matnalopez2/electronica-aplicada-3/Entregables/Recursos/Circuito_ideal_inicial.jpg

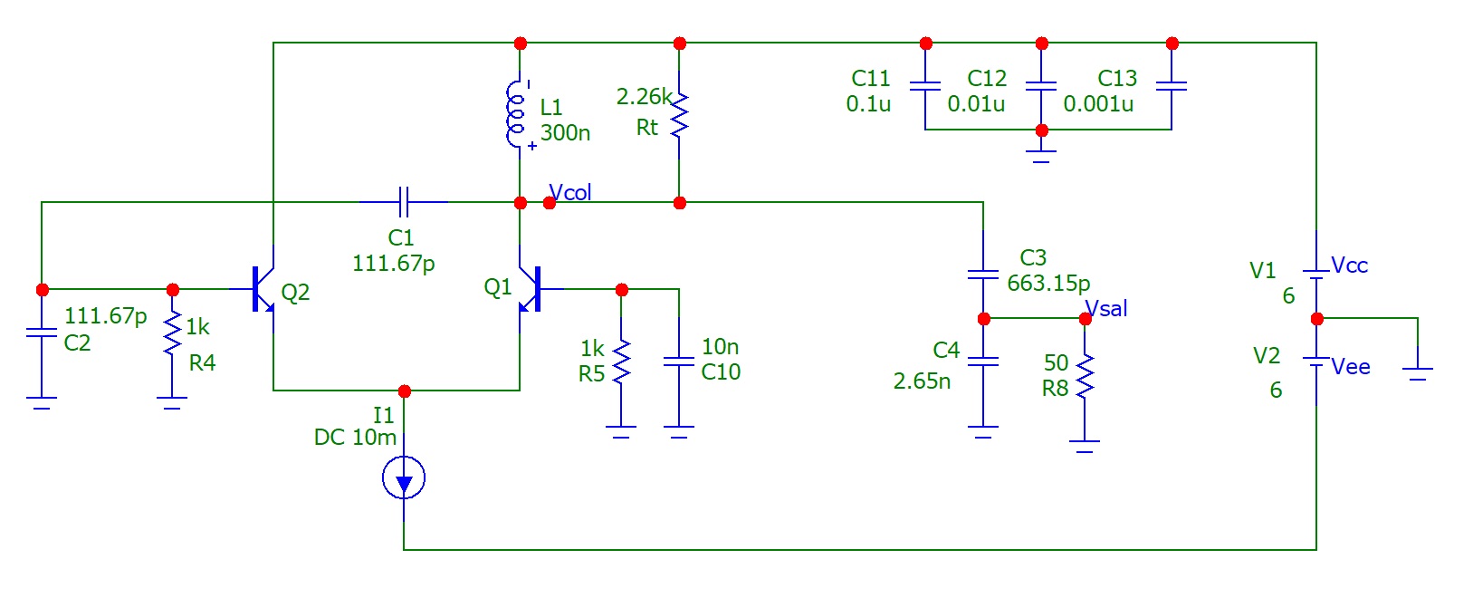
Entregables/Recursos/Circuito_ideal_inicial.jpg
