matnalopez2/electronica-aplicada-3/Recursos/01-Oscilador ideal/01_Circuito_ideal_inicial.jpg

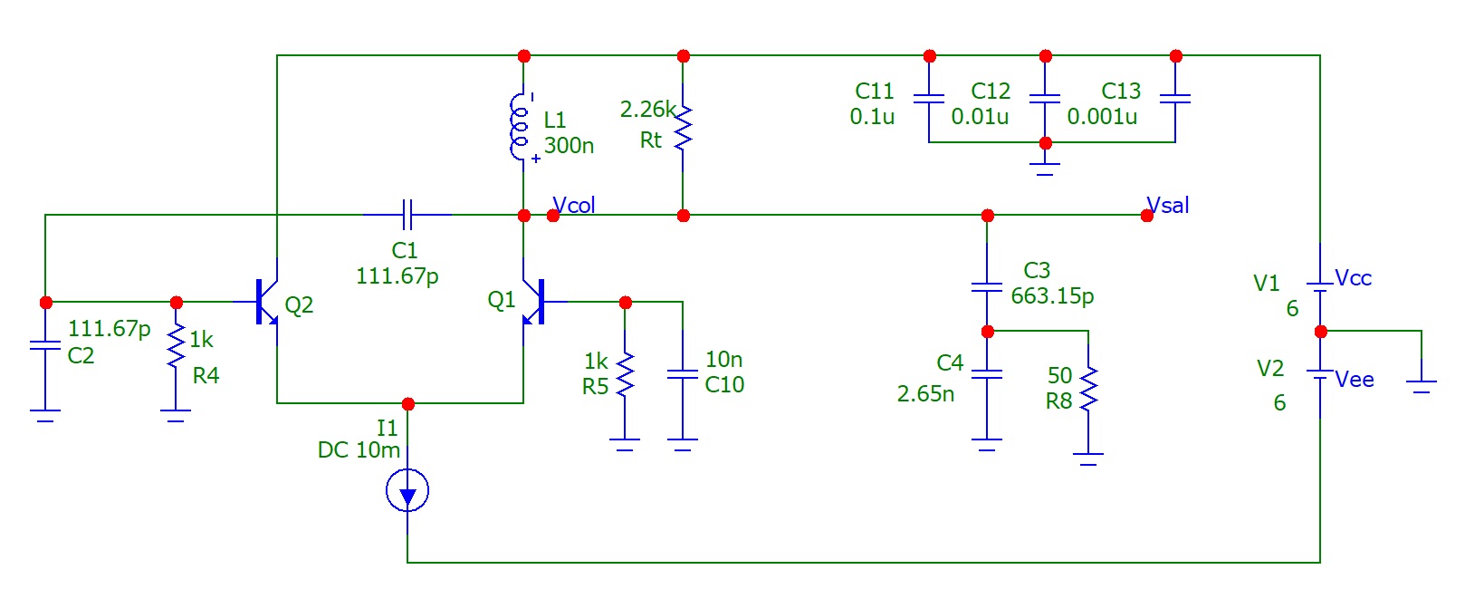
Recursos/01-Oscilador ideal/01_Circuito_ideal_inicial.jpg
