matnalopez2/electronica-aplicada-3/Recursos/01-Oscilador ideal/01_Circuito_ideal_inicial_v2.jpg

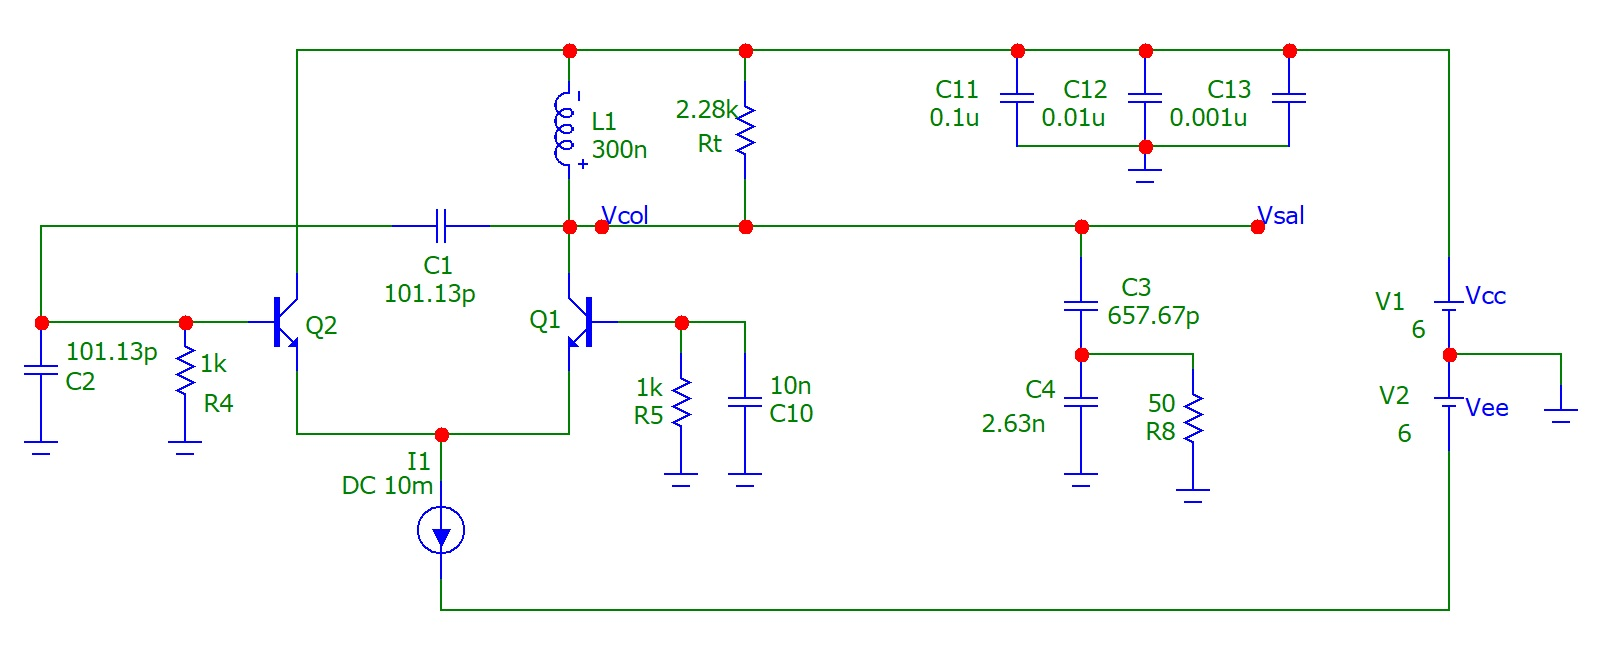
Recursos/01-Oscilador ideal/01_Circuito_ideal_inicial_v2.jpg
