matnalopez2/electronica-aplicada-3/Recursos/01-Oscilador ideal/02_circuito_ideal_con_fuente_ideal_Vcol.jpg

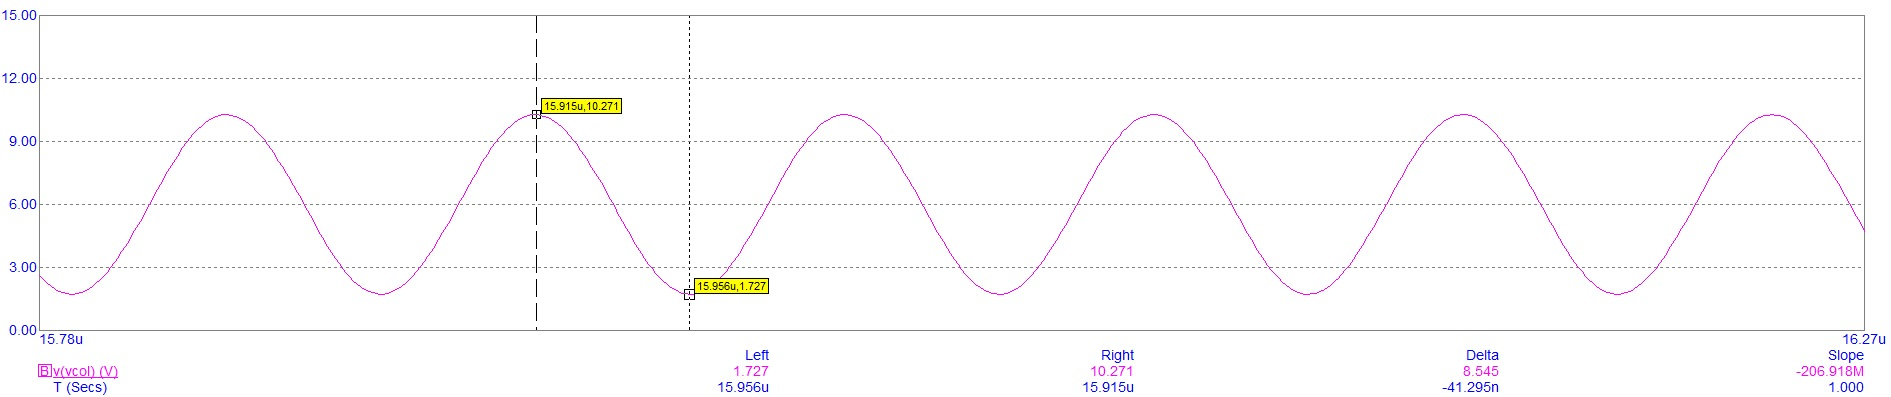
Recursos/01-Oscilador ideal/02_circuito_ideal_con_fuente_ideal_Vcol.jpg
