matnalopez2/electronica-aplicada-3/Recursos/01-Oscilador ideal/03_circuito_ideal_con_fuente_ideal_Vsal.jpg

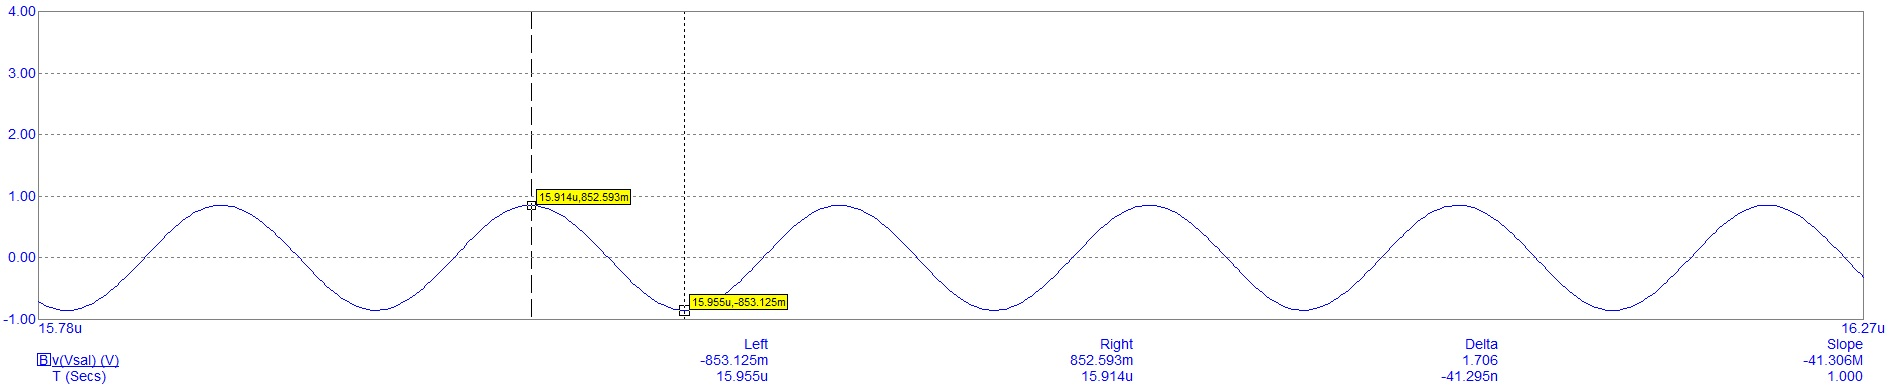
Recursos/01-Oscilador ideal/03_circuito_ideal_con_fuente_ideal_Vsal.jpg
