matnalopez2/electronica-aplicada-3/Recursos/03-Circuito ideal con valores comerciales/03_circuito_ideal_valores_comerciales_Vcol.jpg

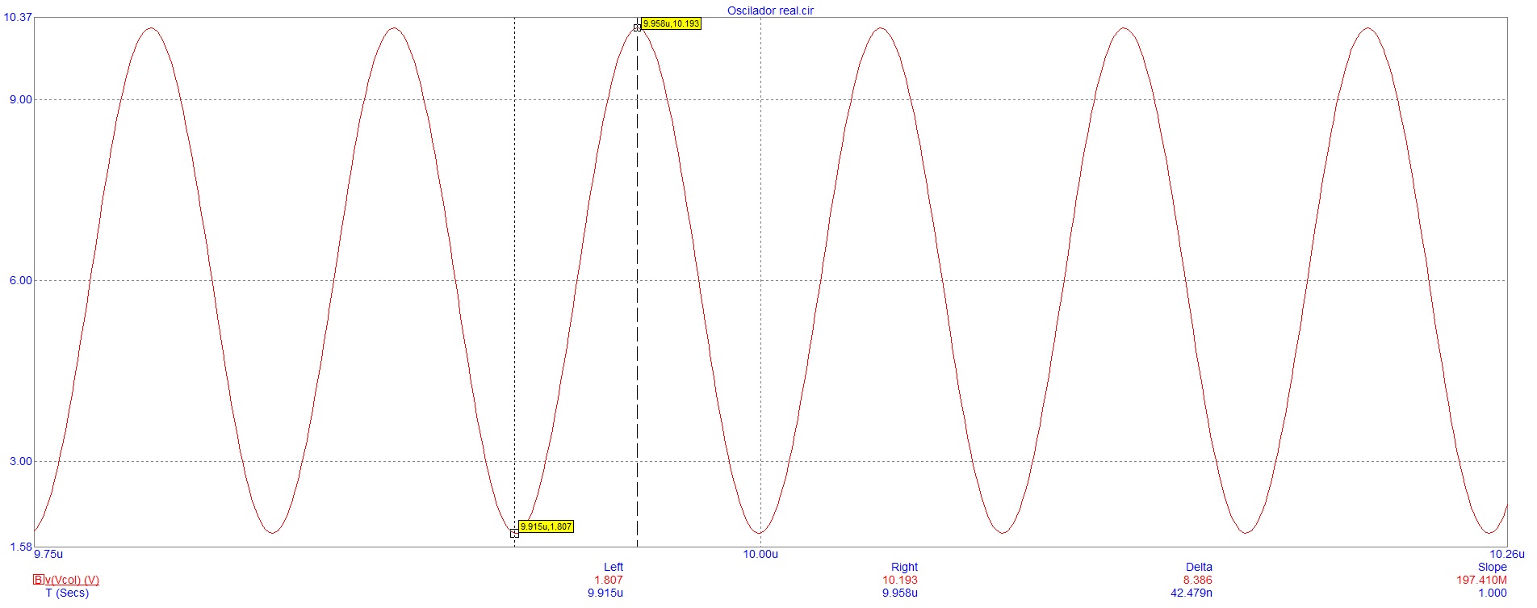
Recursos/03-Circuito ideal con valores comerciales/03_circuito_ideal_valores_comerciales_Vcol.jpg
