matnalopez2/electronica-aplicada-3/Recursos/03-Circuito ideal con valores comerciales/04_circuito_ideal_valores_comerciales_Vsal.jpg

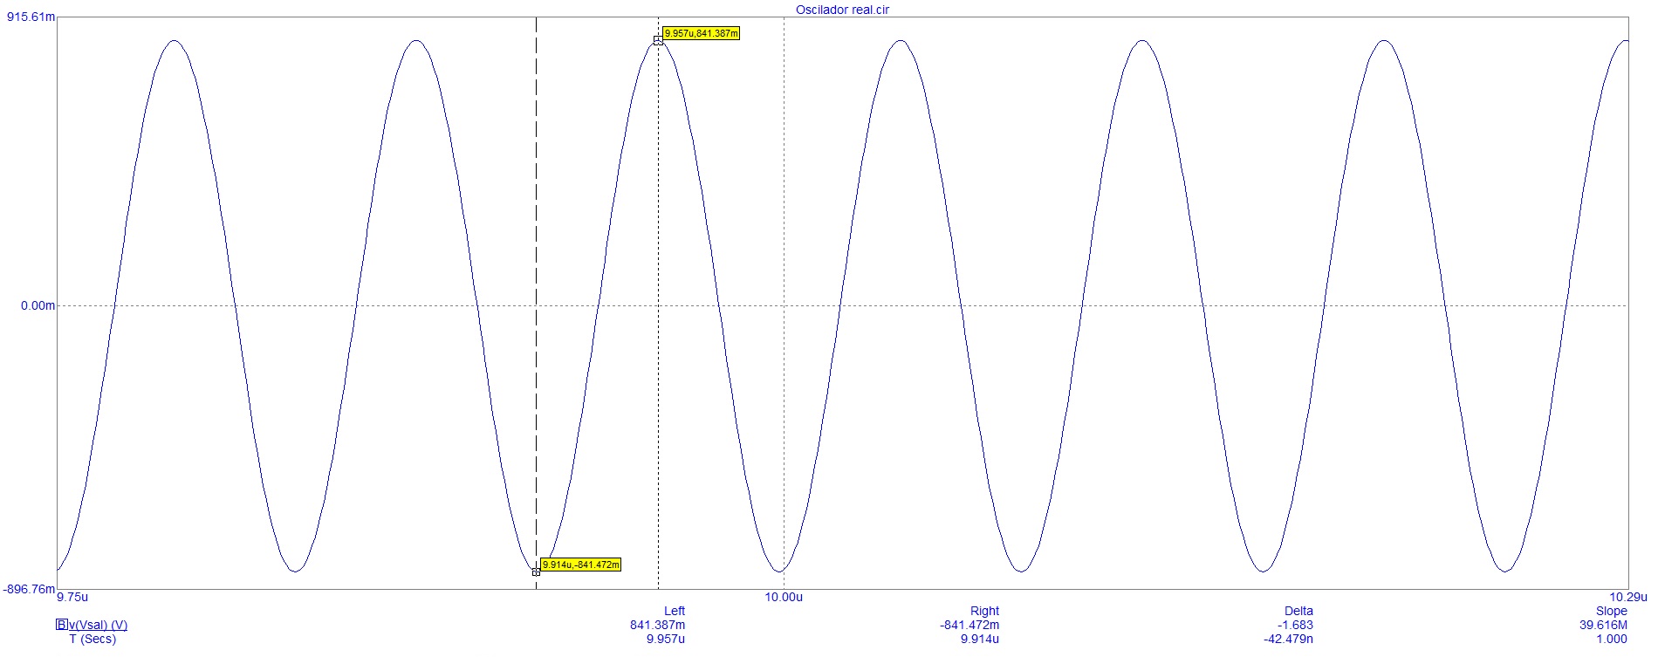
Recursos/03-Circuito ideal con valores comerciales/04_circuito_ideal_valores_comerciales_Vsal.jpg
