matnalopez2/electronica-aplicada-3/Recursos/05-Oscilador con mediciones FRA/01_esquematico.jpg

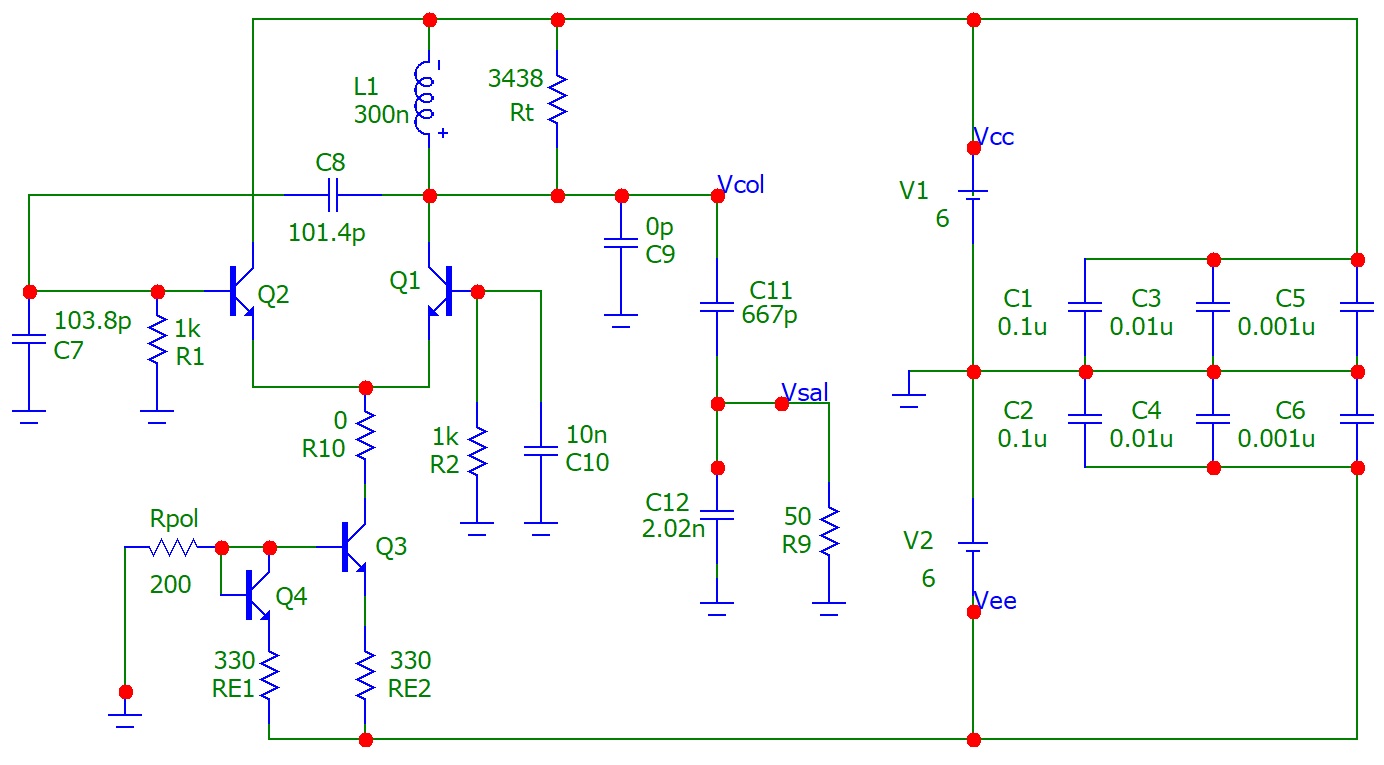
Recursos/05-Oscilador con mediciones FRA/01_esquematico.jpg
