matnalopez2/electronica-aplicada-3/Recursos/05-Oscilador con mediciones FRA/03_colector_transientConFrecuencia.jpg

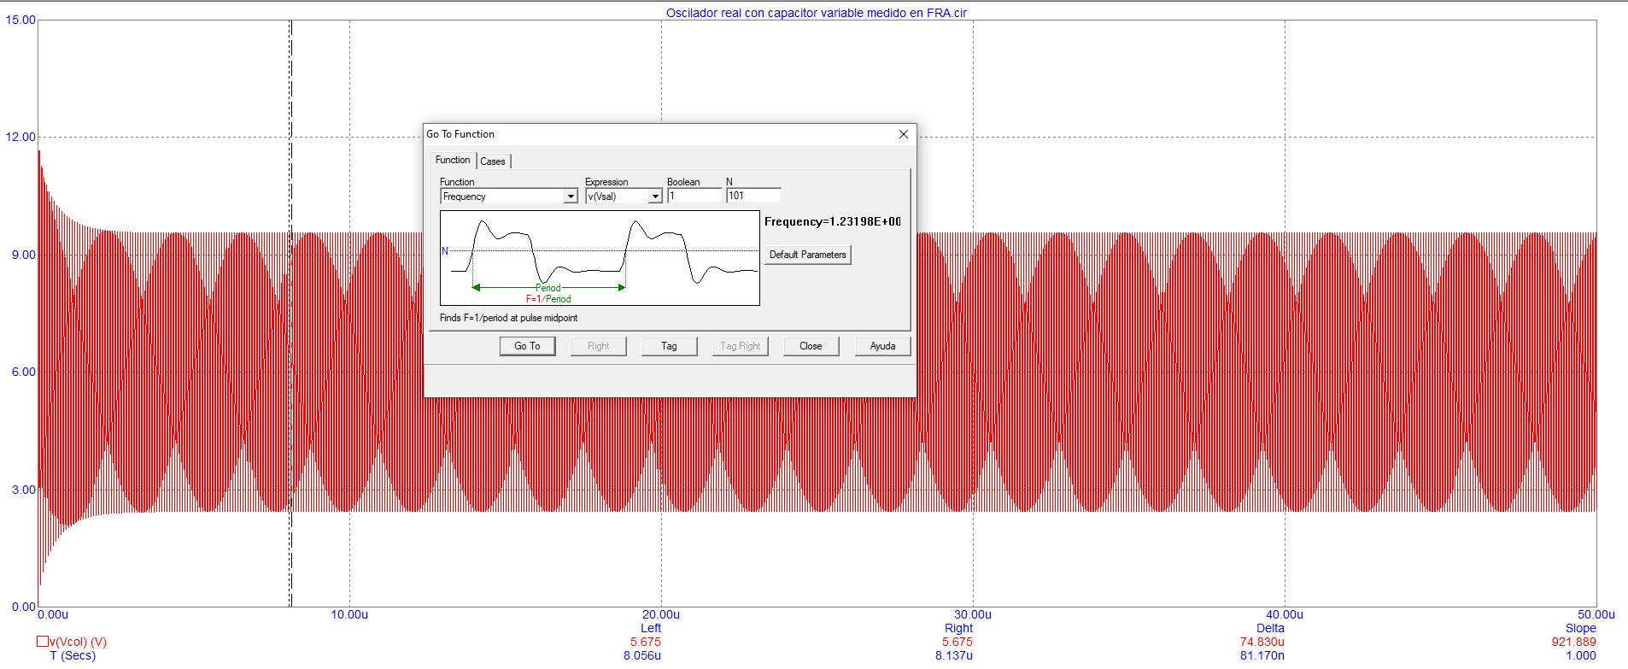
Recursos/05-Oscilador con mediciones FRA/03_colector_transientConFrecuencia.jpg
