matnalopez2/electronica-aplicada-3/Recursos/05-Oscilador con mediciones FRA/04_colector_frecuencia.jpg

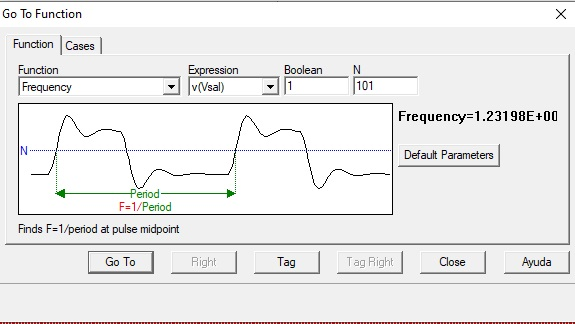
Recursos/05-Oscilador con mediciones FRA/04_colector_frecuencia.jpg
