matnalopez2/electronica-aplicada-3/Recursos/05-Oscilador con mediciones FRA/05_colector_cicloConCursores.jpg

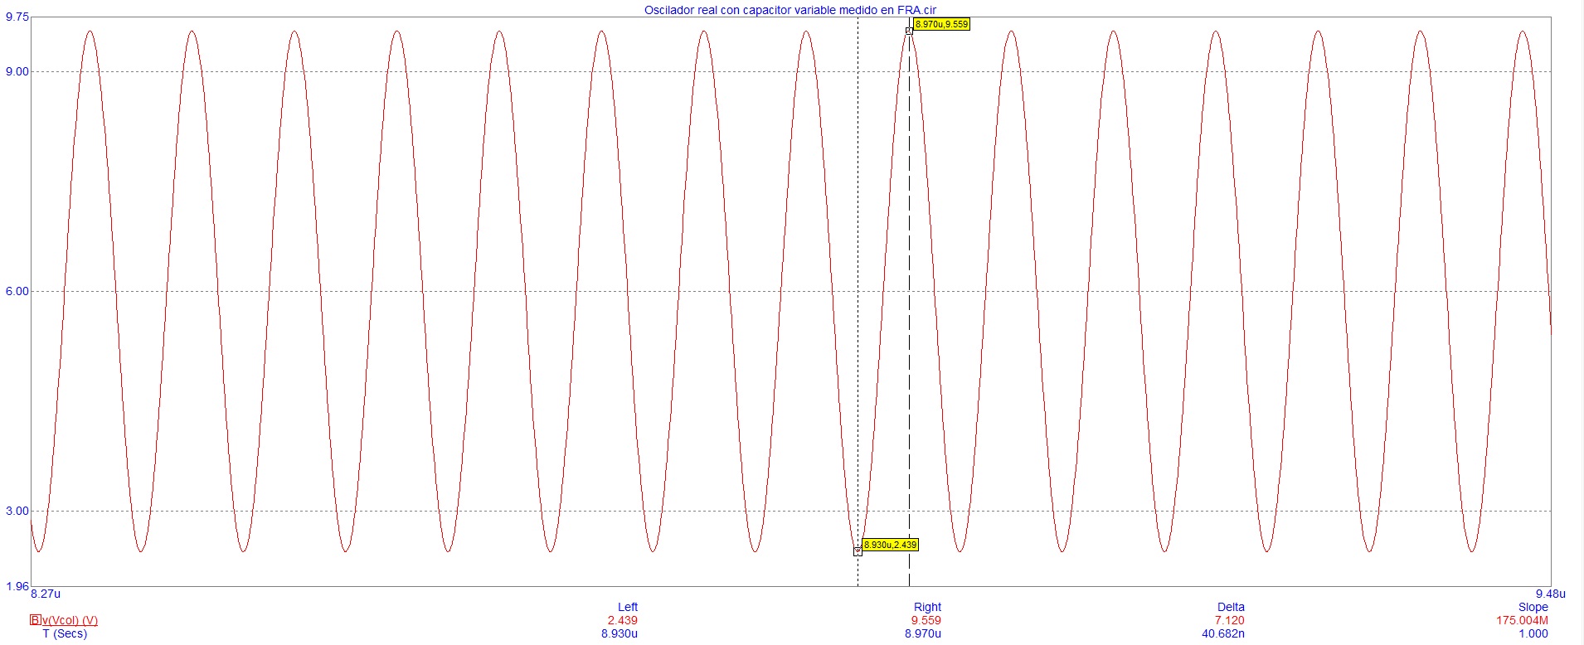
Recursos/05-Oscilador con mediciones FRA/05_colector_cicloConCursores.jpg
