matnalopez2/electronica-aplicada-3/Recursos/05-Oscilador con mediciones FRA/06_colector_cicloConFrecuencia.jpg

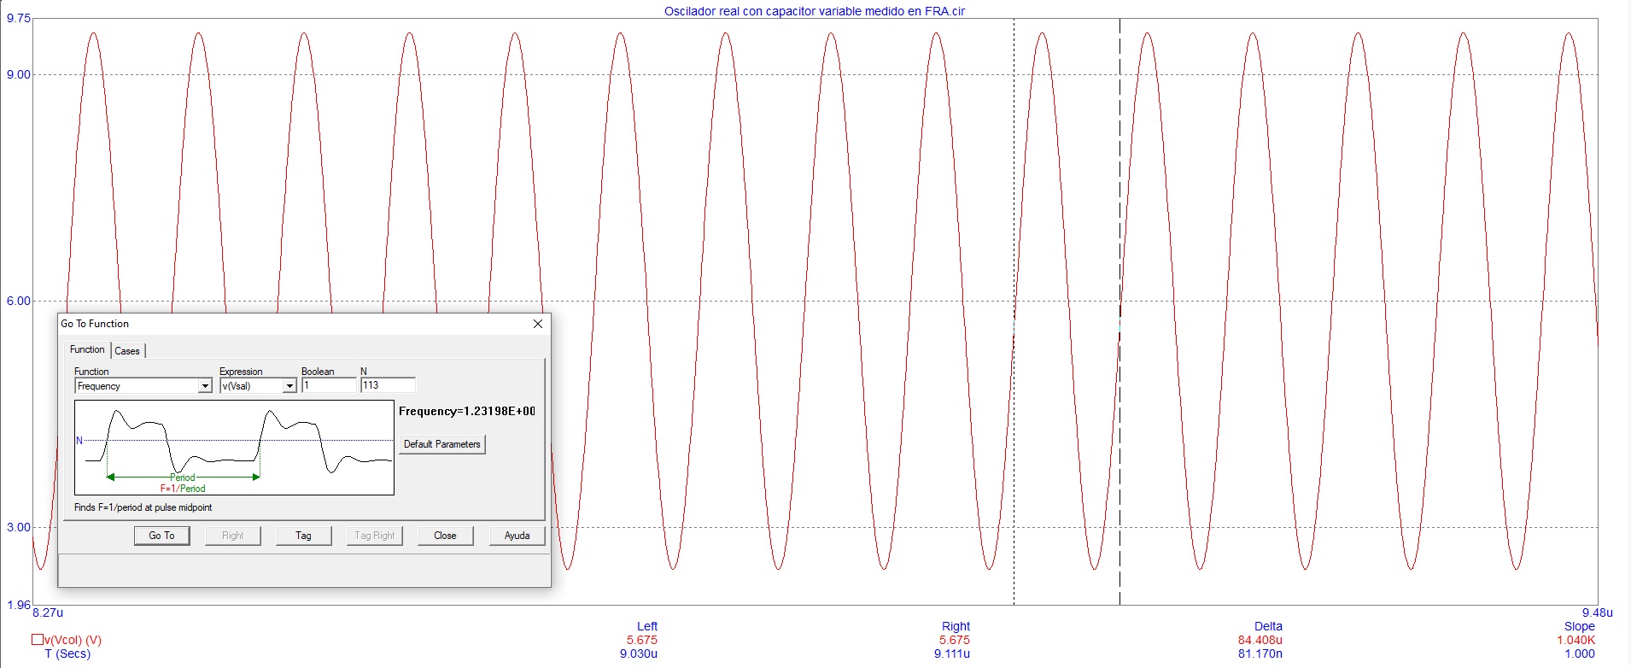
Recursos/05-Oscilador con mediciones FRA/06_colector_cicloConFrecuencia.jpg
