matnalopez2/electronica-aplicada-3/Recursos/05-Oscilador con mediciones FRA/07_colector_picosPositivos.jpg

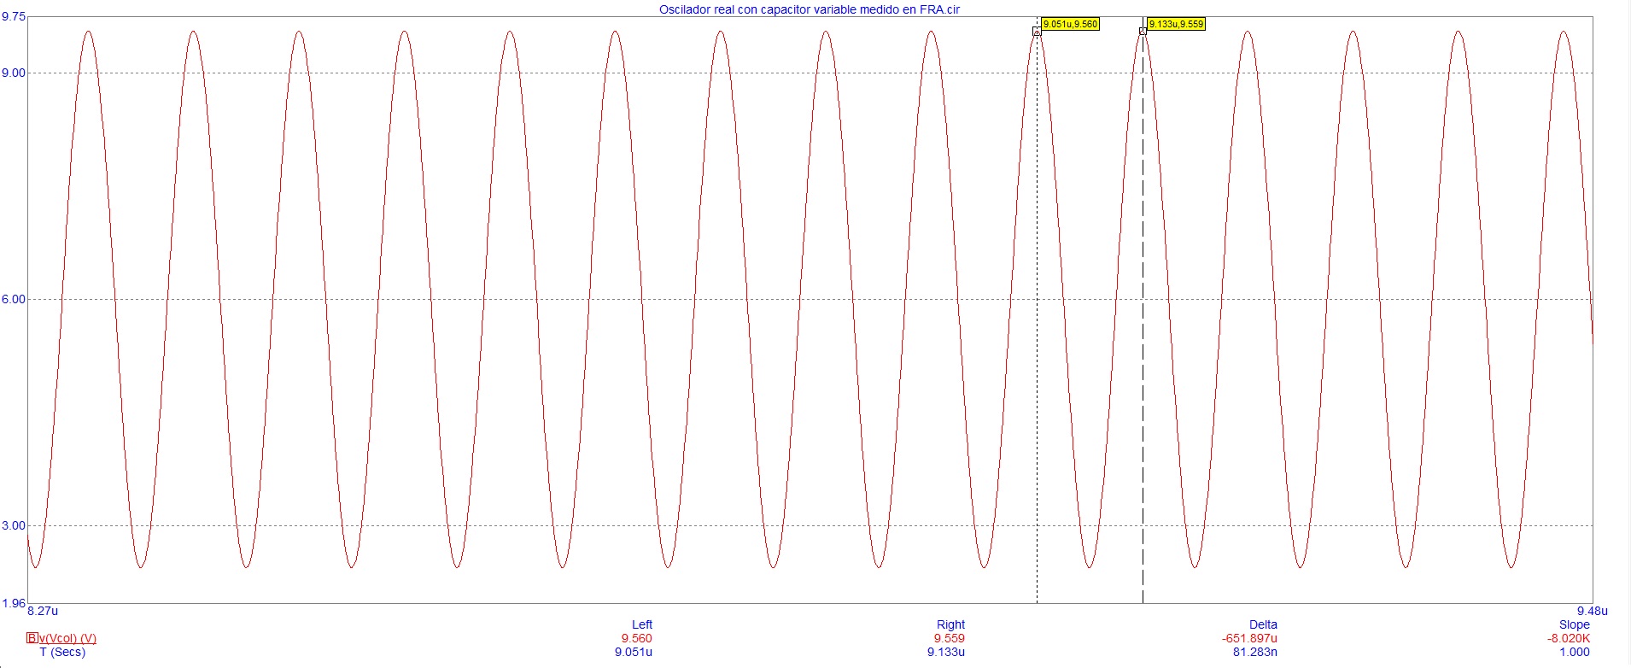
Recursos/05-Oscilador con mediciones FRA/07_colector_picosPositivos.jpg
