matnalopez2/electronica-aplicada-3/Recursos/05-Oscilador con mediciones FRA/08_salida_transient.jpg

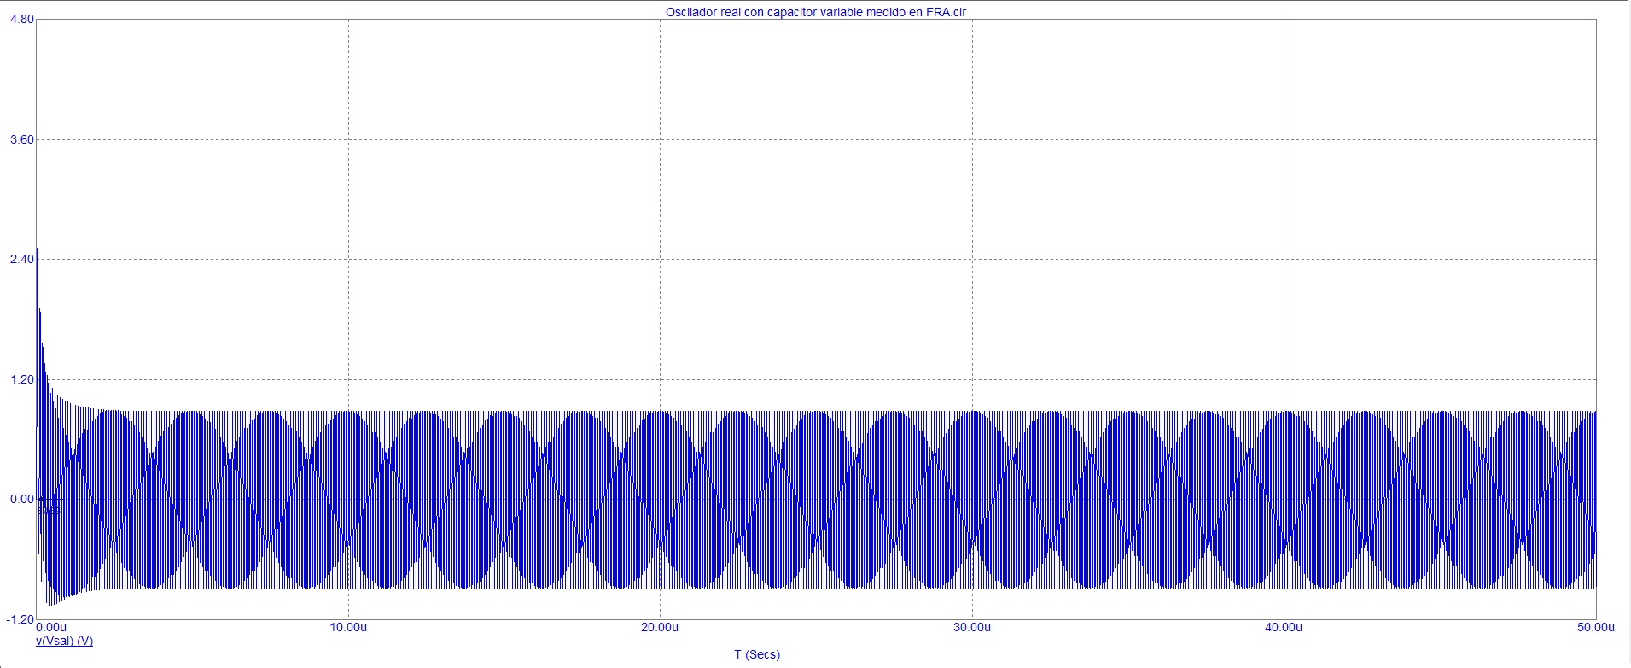
Recursos/05-Oscilador con mediciones FRA/08_salida_transient.jpg
