matnalopez2/electronica-aplicada-3/Recursos/05-Oscilador con mediciones FRA/11_salida_cicloConCursores.jpg

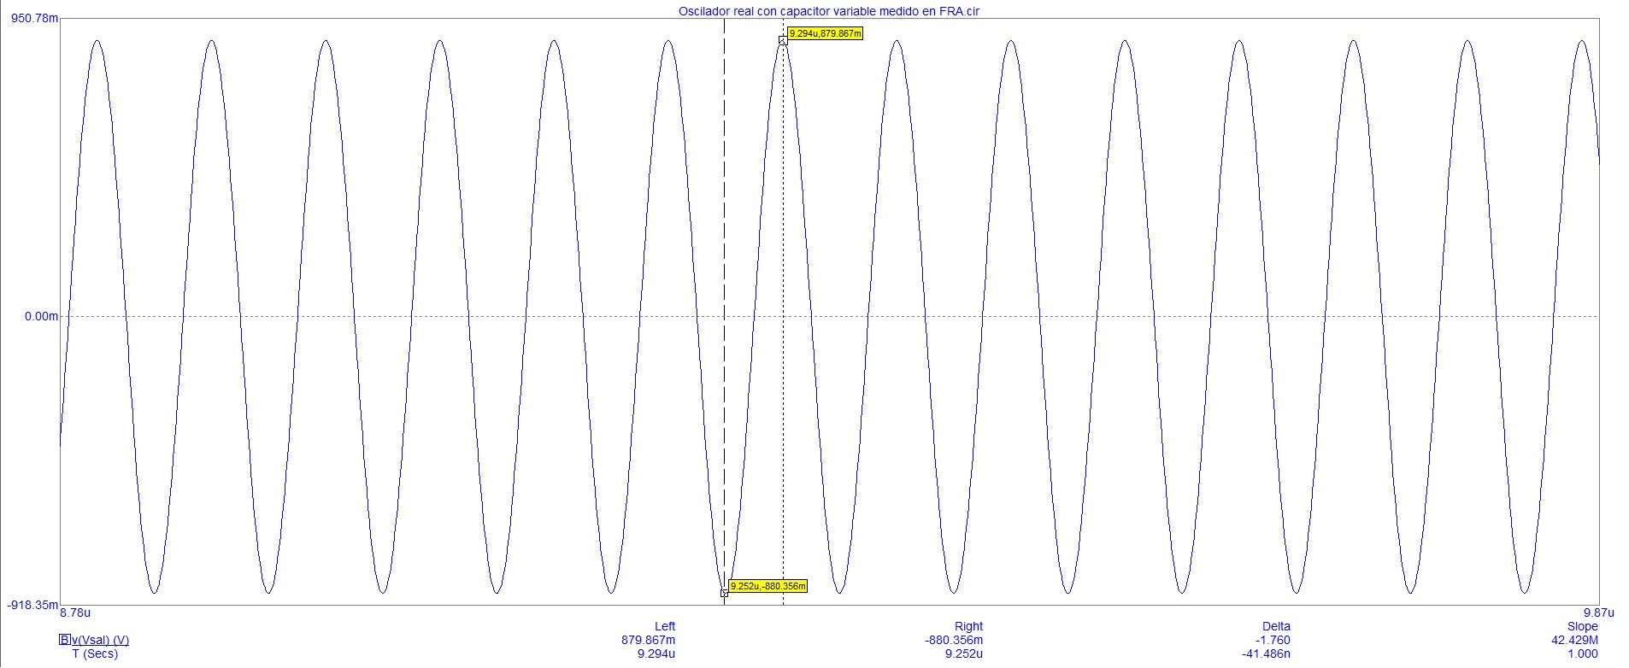
Recursos/05-Oscilador con mediciones FRA/11_salida_cicloConCursores.jpg
