matnalopez2/electronica-aplicada-3/Recursos/05-Oscilador con mediciones FRA/12_salida_cicloConFrecuencia.jpg

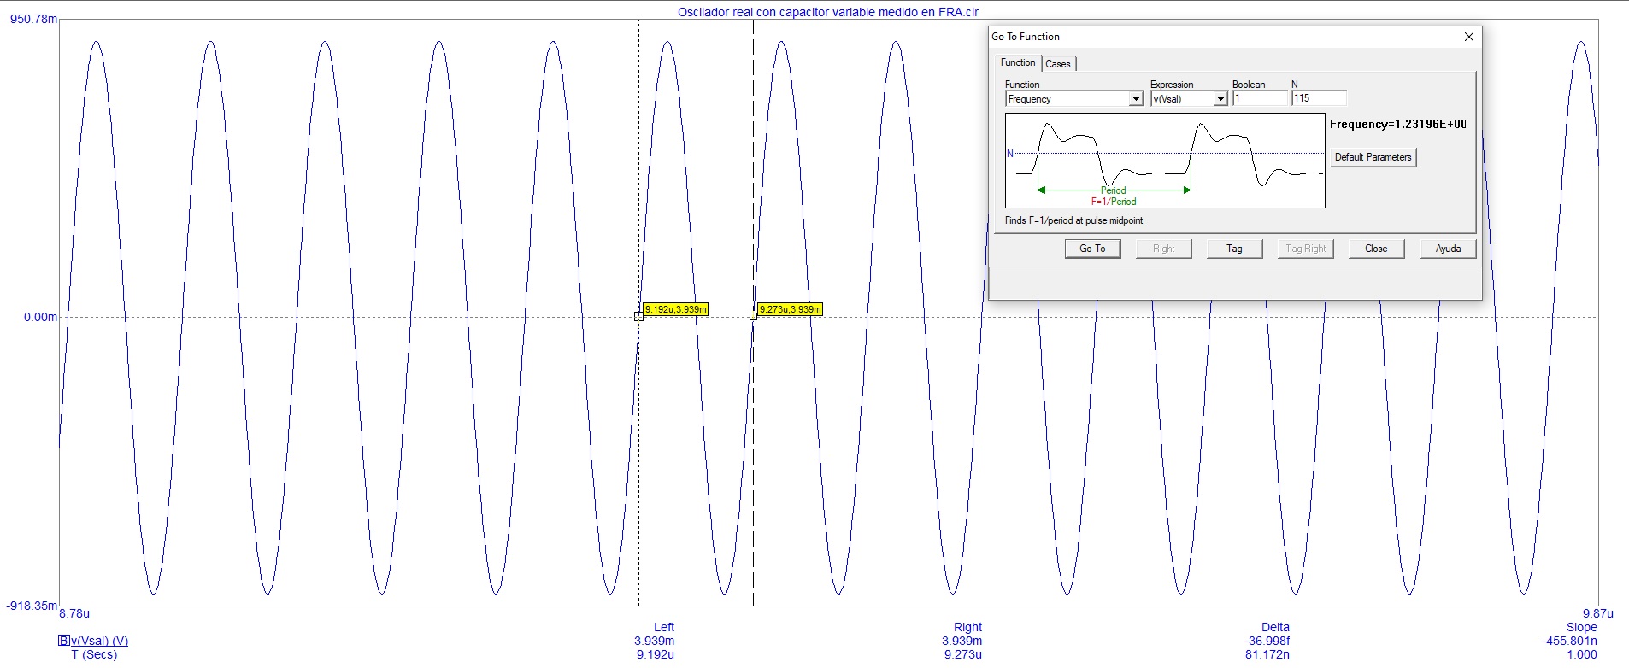
Recursos/05-Oscilador con mediciones FRA/12_salida_cicloConFrecuencia.jpg
