matnalopez2/electronica-aplicada-3/Recursos/05-Oscilador con mediciones FRA/13_salida_picosPositivos.jpg

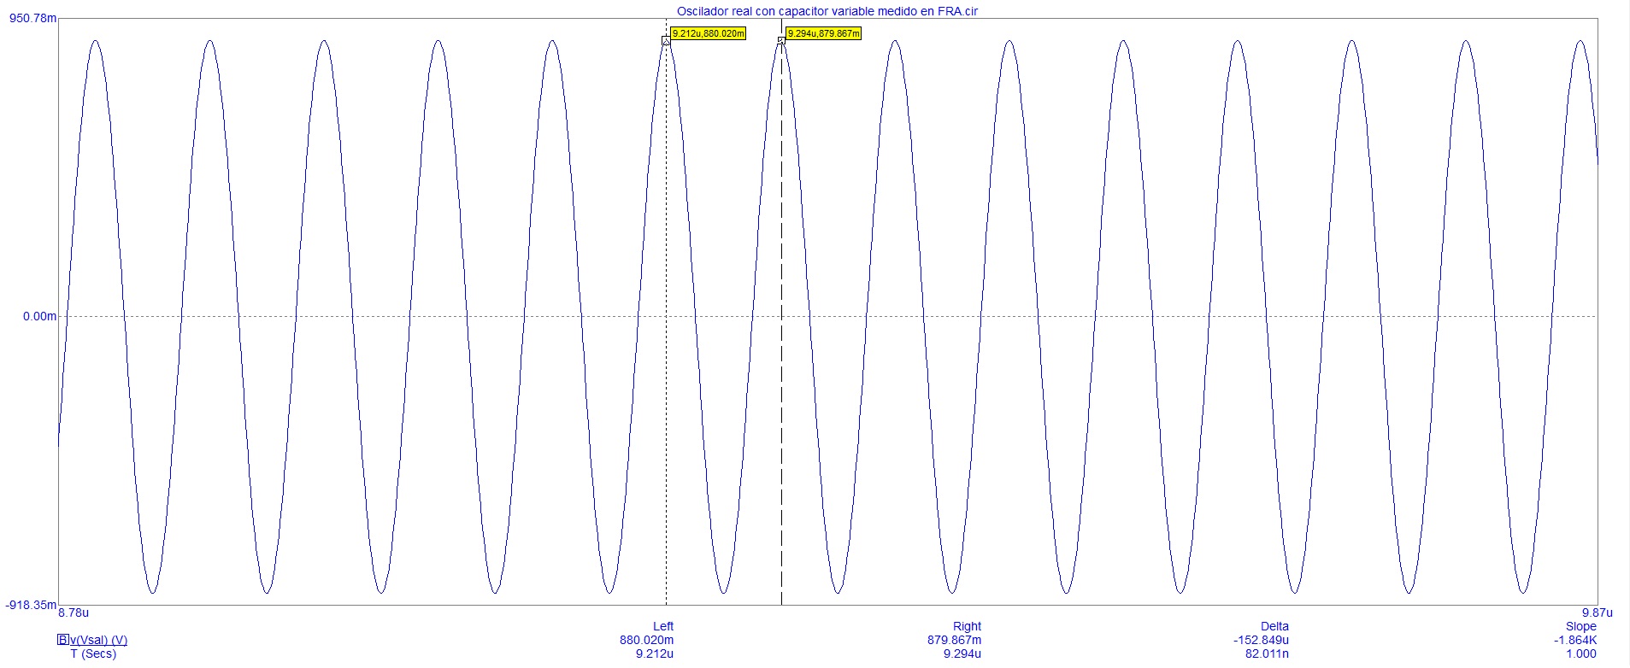
Recursos/05-Oscilador con mediciones FRA/13_salida_picosPositivos.jpg
