matnalopez2/electronica-aplicada-3/Recursos/06-Placa terminada/01_placaSuperior.jpeg

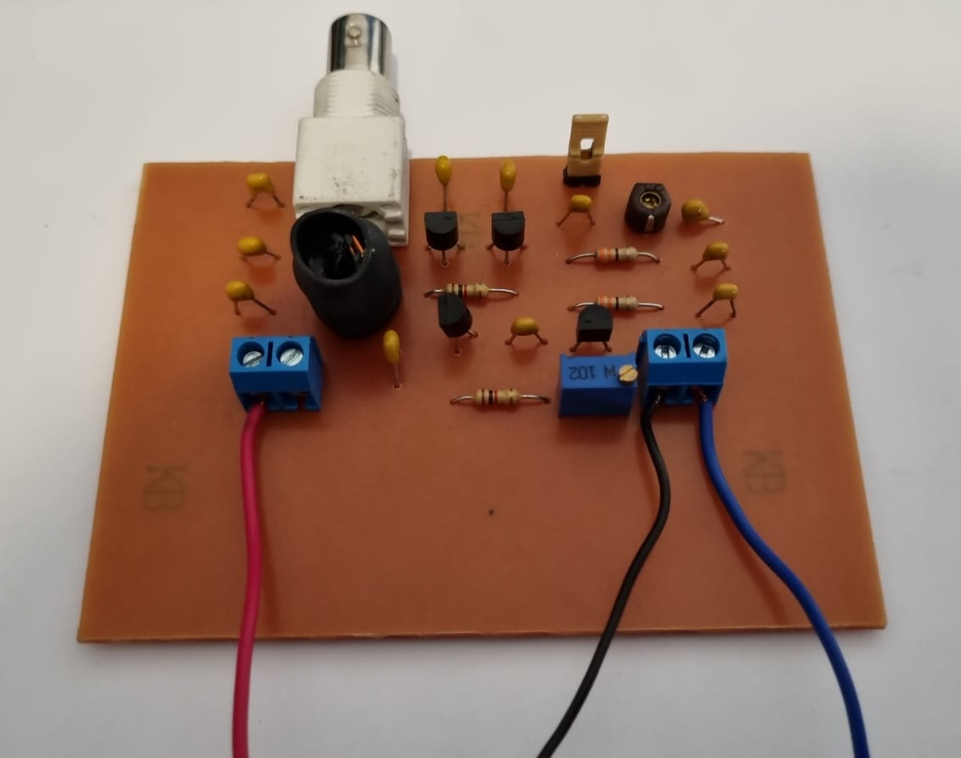
Recursos/06-Placa terminada/01_placaSuperior.jpeg
