matnalopez2/electronica-aplicada-3/Recursos/06-Placa terminada/03_placaPistas.jpeg

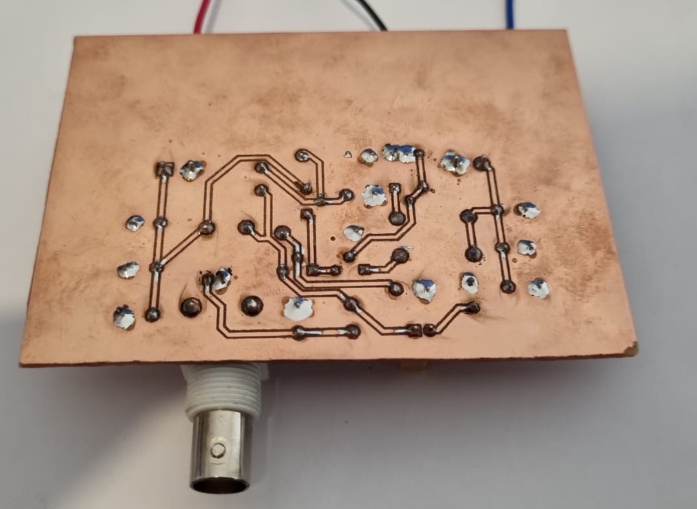
Recursos/06-Placa terminada/03_placaPistas.jpeg
