matnalopez2/electronica-aplicada-3/Recursos/06-Placa terminada/04_placaPistas.jpeg

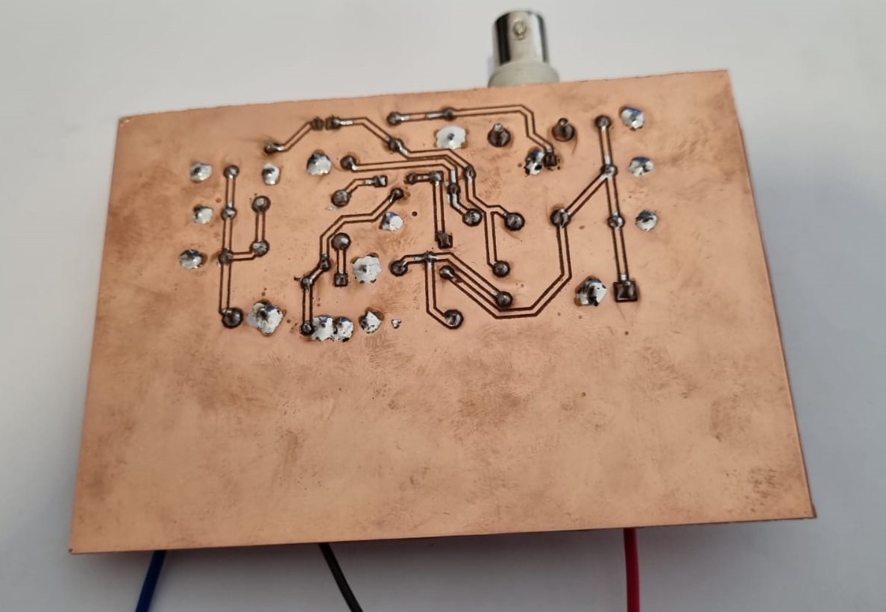
Recursos/06-Placa terminada/04_placaPistas.jpeg
