matnalopez2/electronica-aplicada-3/Recursos/07-Mediciones/1.jpeg

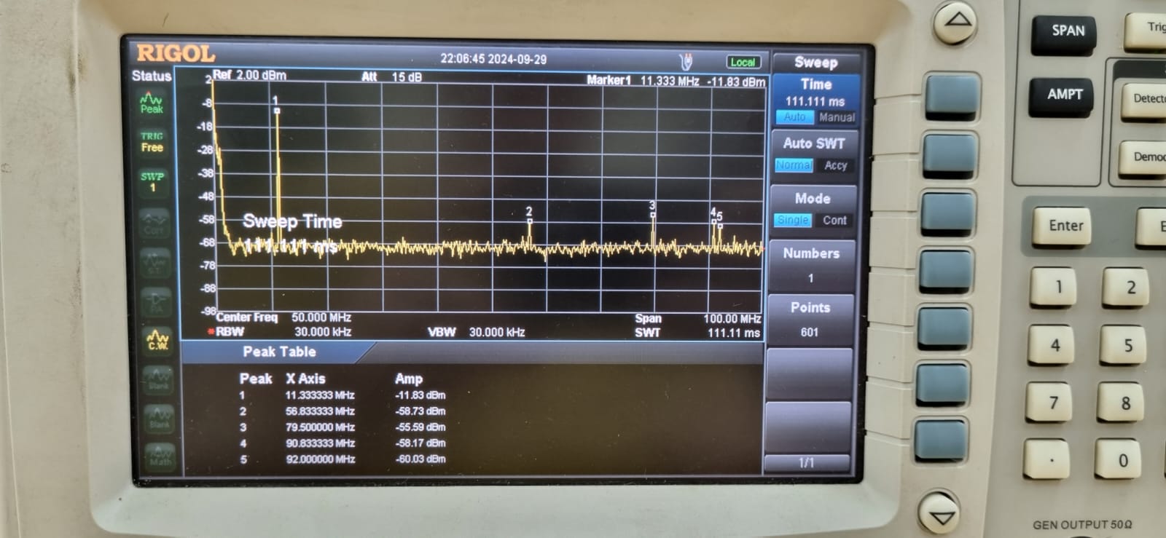
Recursos/07-Mediciones/1.jpeg
