matnalopez2/electronica-aplicada-3/Recursos/07-Mediciones/3.jpeg

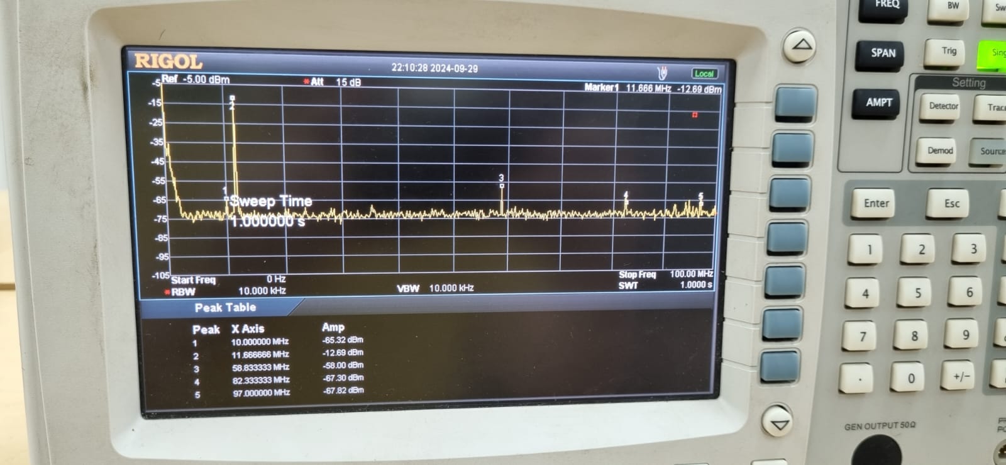
Recursos/07-Mediciones/3.jpeg
