matnalopez2/electronica-aplicada-3/Recursos/07-Mediciones/4_placaSinJumper.jpeg

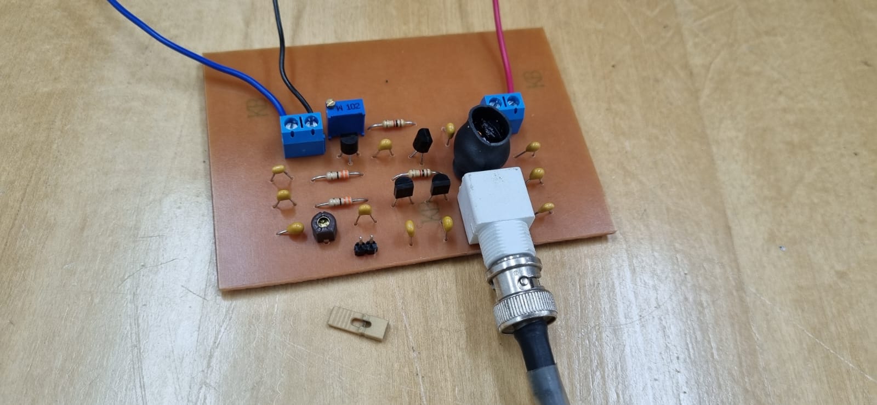
Recursos/07-Mediciones/4_placaSinJumper.jpeg
