matnalopez2/electronica-aplicada-3/Recursos/07-Mediciones/6_instrumentos.jpeg

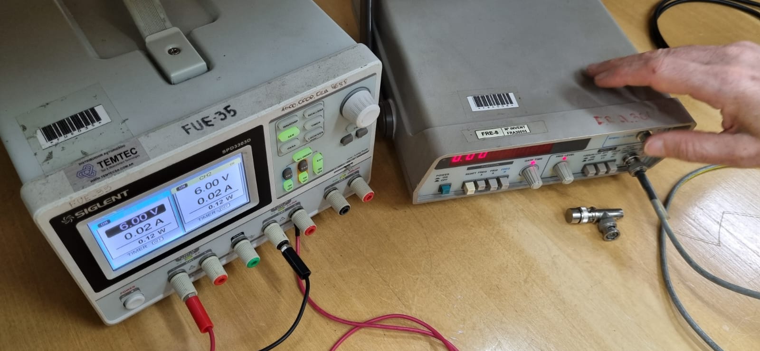
Recursos/07-Mediciones/6_instrumentos.jpeg
