matnalopez2/electronica-aplicada-3/Recursos/07-Mediciones/7_instrumentos.jpeg

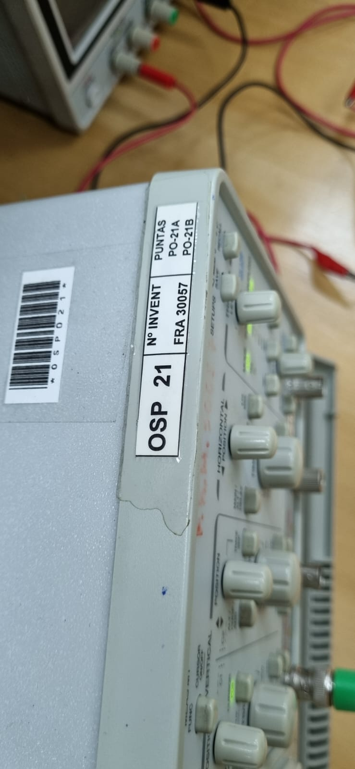
Recursos/07-Mediciones/7_instrumentos.jpeg
