matnalopez2/electronica-aplicada-3/Recursos/07-Mediciones/8_frecuencimetroMaximo.jpeg

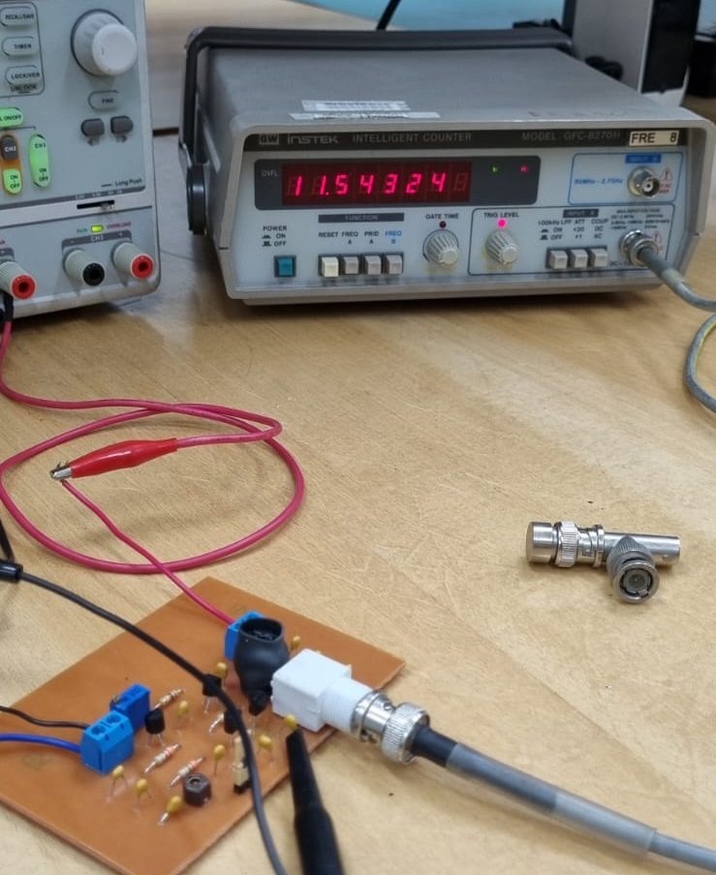
Recursos/07-Mediciones/8_frecuencimetroMaximo.jpeg
