matnalopez2/electronica-aplicada-3/Recursos/07-Mediciones/9_frecuencimetroMinimo.jpeg

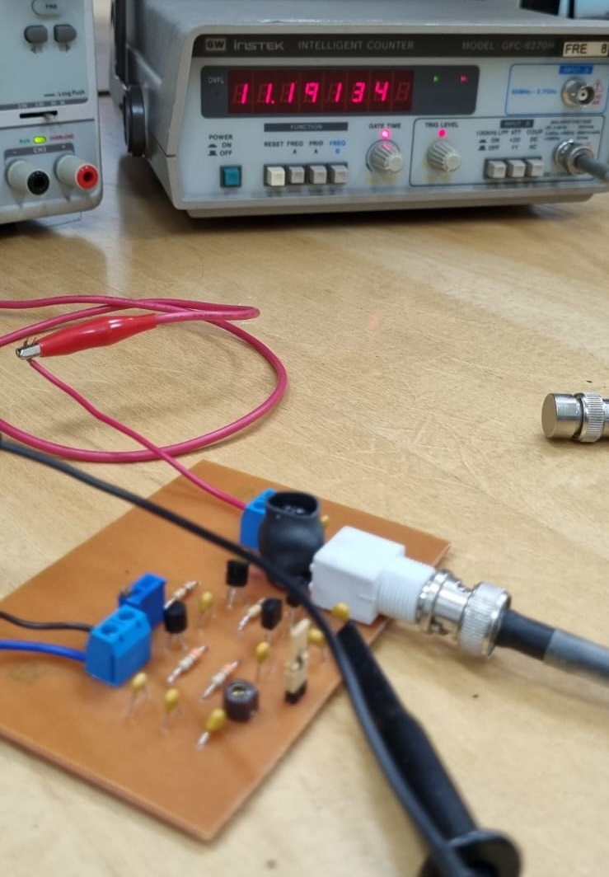
Recursos/07-Mediciones/9_frecuencimetroMinimo.jpeg
