matnalopez2/electronica-aplicada-3/Recursos/caratulaTP.jpg

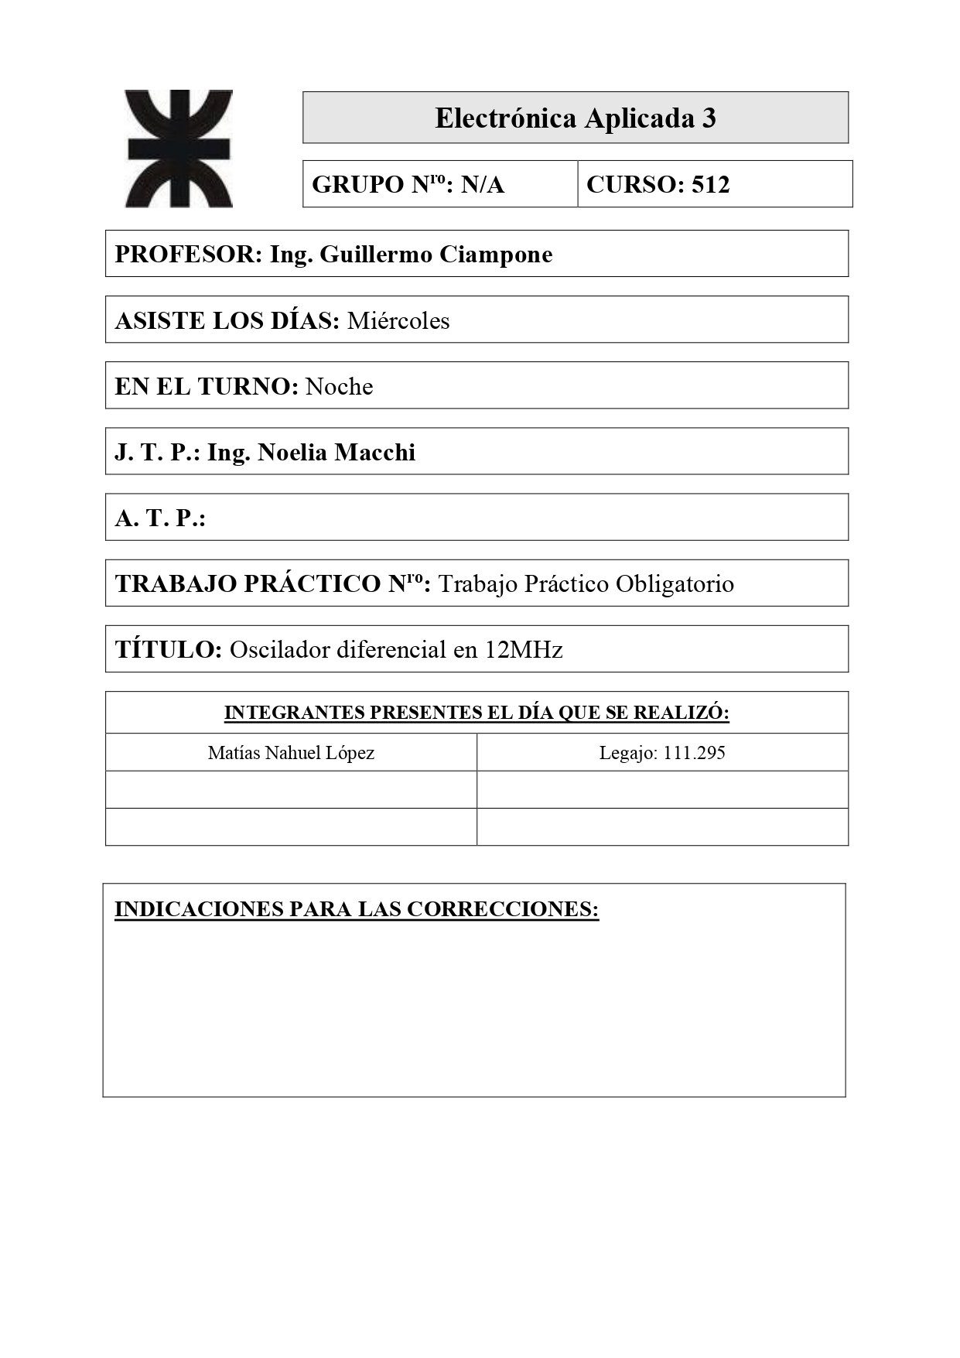
Recursos/caratulaTP.jpg
