matnalopez2/electronica-aplicada-3/Recursos/Circuito_referencia.png

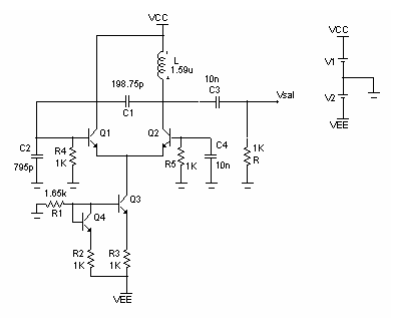
Recursos/Circuito_referencia.png
