matnalopez2/electronica-aplicada-3/Recursos/Esquematico.png

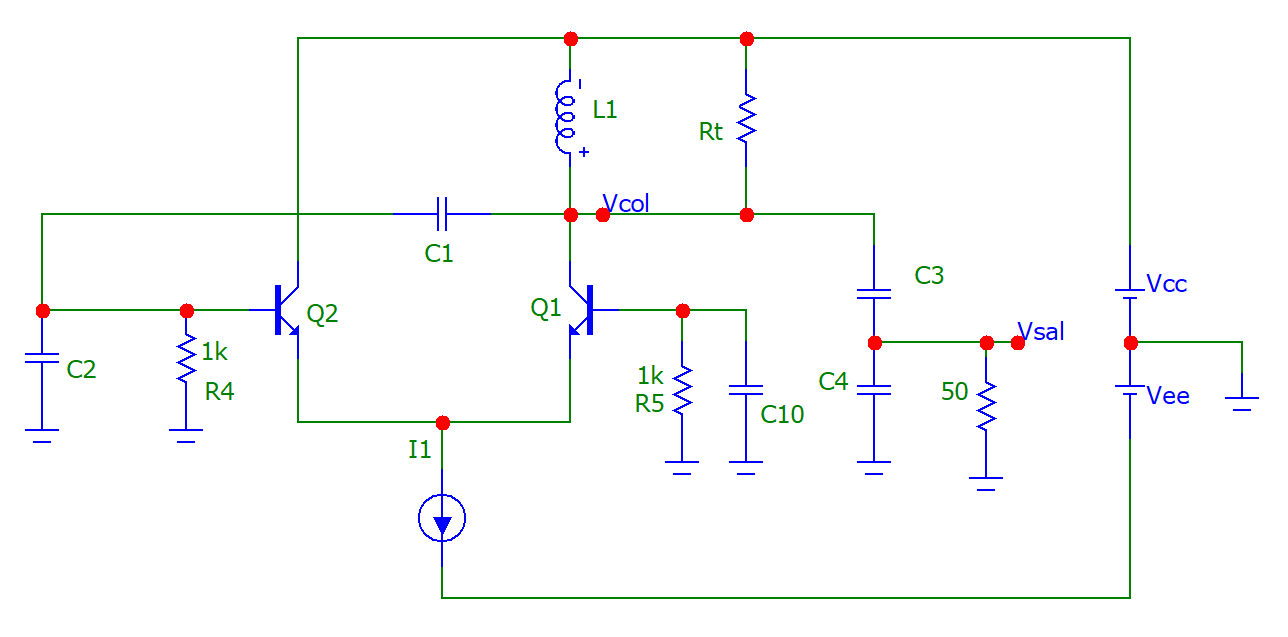
Recursos/Esquematico.png
