matnalopez2/electronica-aplicada-3/Recursos/Kicad/esquematico_capacitores.jpg

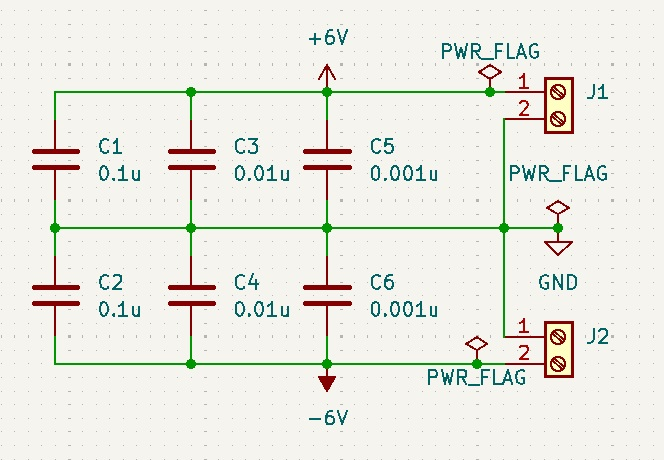
Recursos/Kicad/esquematico_capacitores.jpg
