matnalopez2/electronica-aplicada-3/Recursos/Kicad/esquematico_circuito.jpg

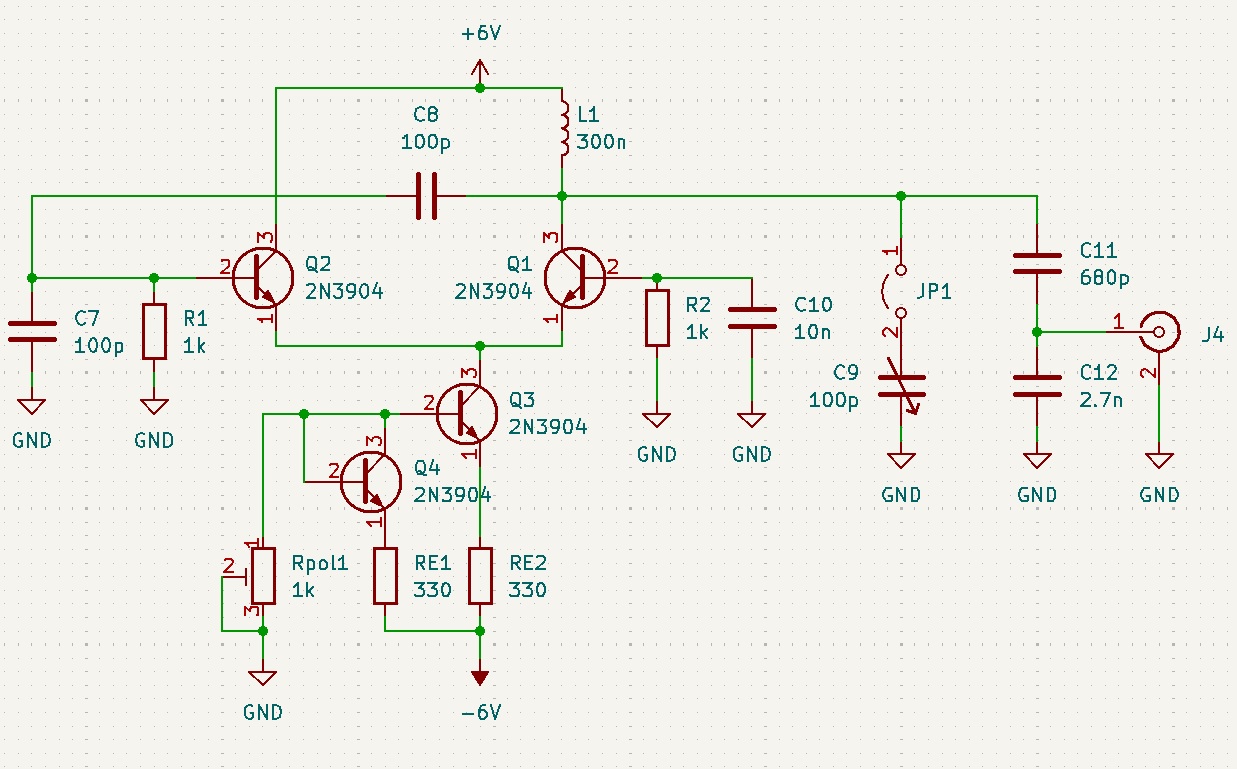
Recursos/Kicad/esquematico_circuito.jpg
