matnalopez2/electronica-aplicada-3/Recursos/Kicad/pcb_ruteo_03.jpg

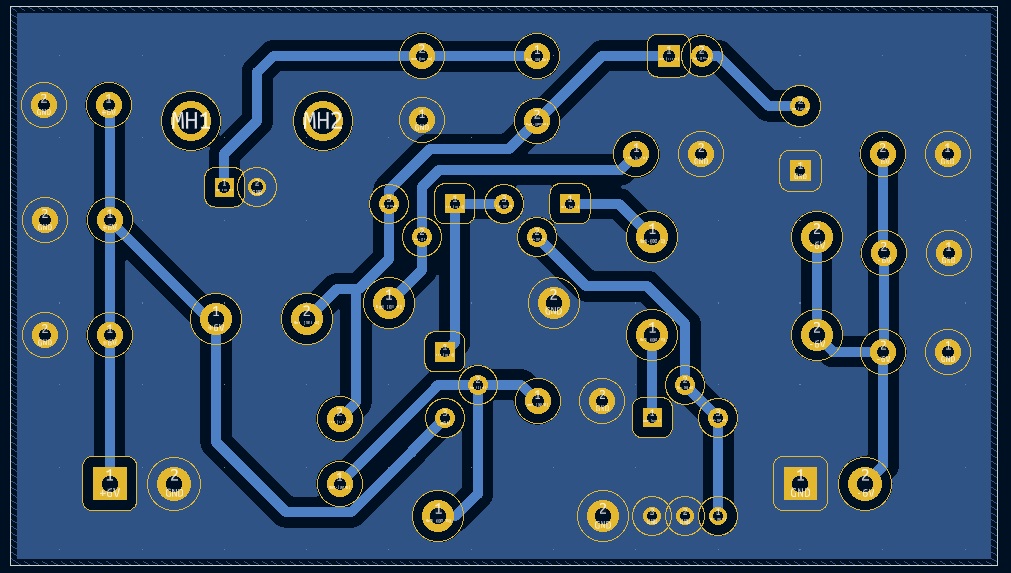
Recursos/Kicad/pcb_ruteo_03.jpg
