matnalopez2/electronica-aplicada-3/Recursos/Kicad/vista_3d_superior.jpg

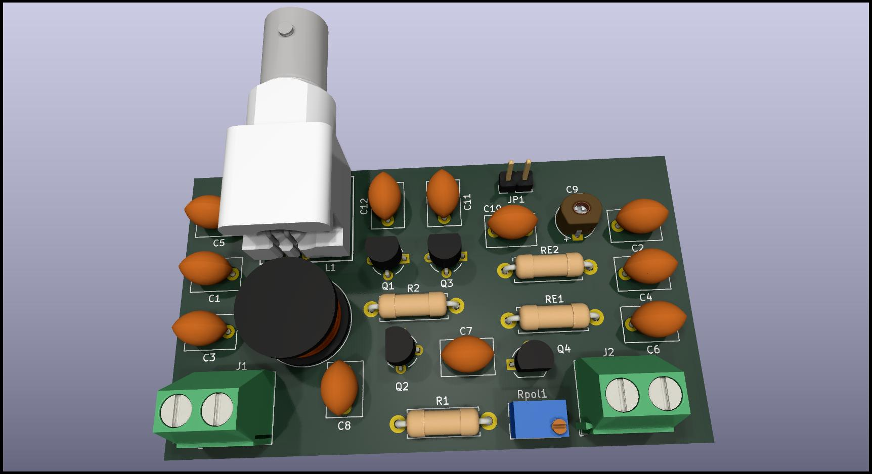
Recursos/Kicad/vista_3d_superior.jpg
