matnalopez2/electronica-aplicada-3/Recursos/01-Oscilador ideal/04_circuito_ideal_con_fuente_ideal_performance_v2.jpg

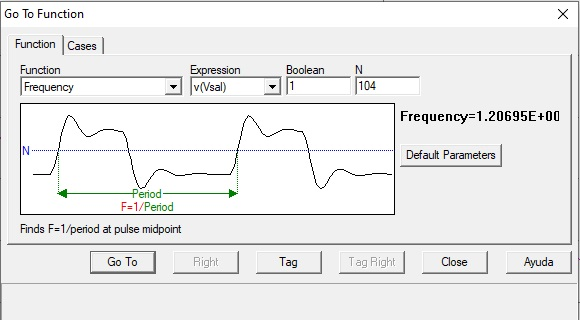
Recursos/01-Oscilador ideal/04_circuito_ideal_con_fuente_ideal_performance_v2.jpg
