matnalopez2/electronica-aplicada-3/Recursos/03-Circuito ideal con valores comerciales/02_circuito_ideal_valores_comerciales_performance.jpg

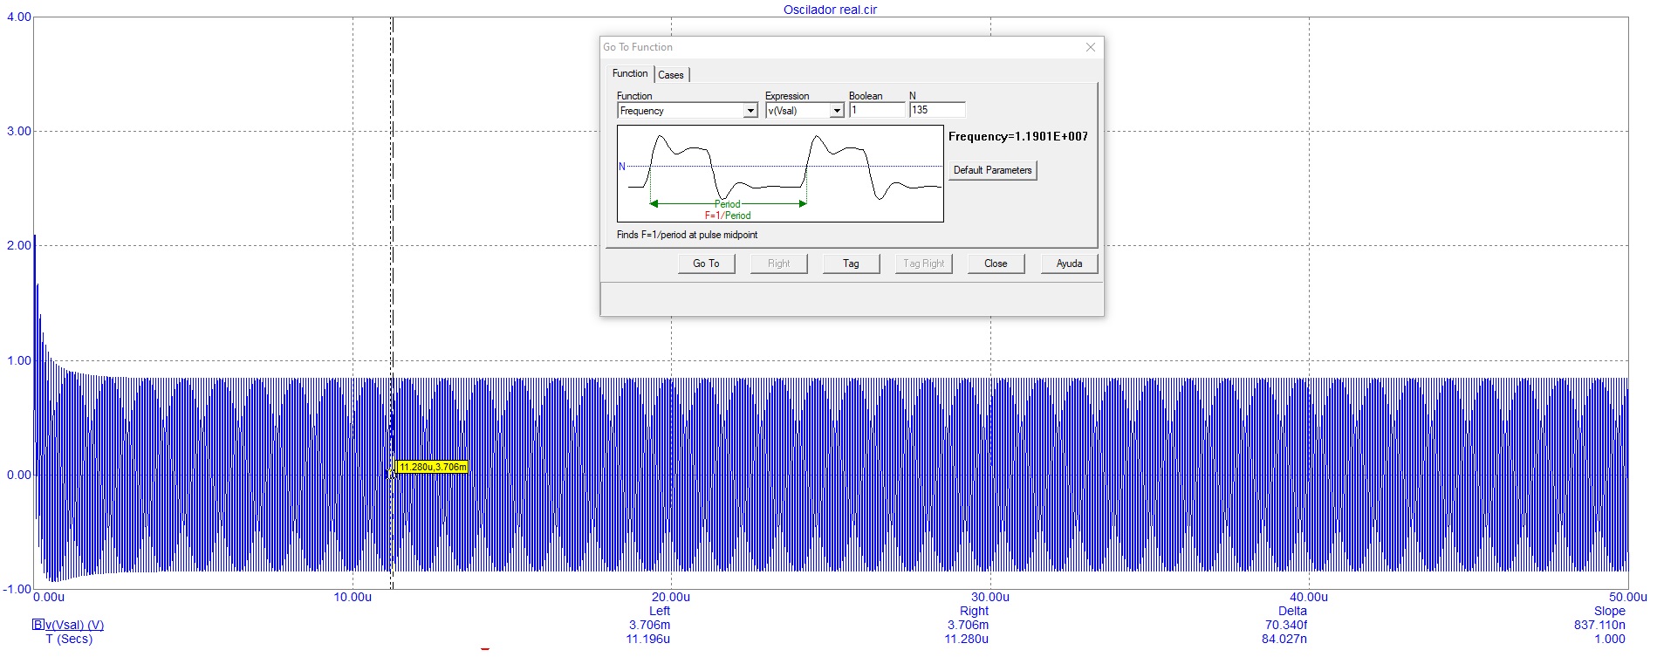
Recursos/03-Circuito ideal con valores comerciales/02_circuito_ideal_valores_comerciales_performance.jpg
