matnalopez2/electronica-aplicada-3/Microcap/Oscilador real con capacitor variable medido en FRA.cir

[Main]
FileType=CIR
Version=12.00
Program=Micro-Cap
Component Version=10.00
Shape Version=11.00
Screen=1920,1080
MCAPVersion=12.2.0.5
Key ID=Demo
NLCnt=101
TXCnt=4

[shapedef]
Name=Battery
Line=0,0,22,0
Line=22,-3,22,3
Line=26,-7,26,7
Line=26,0,48,0
Current=32,8,16,8

[shapedef]
Name=Bjt.root
Line=0,0,13,0
Rectangle=13,-12,15,12
Current=32,-24,32,-16
Current=32,24,32,16
Current=0,-8,8,-8
PolyOpen=3
PolyLine=24,-24
PolyLine=24,-12
PolyLine=14,-2
PolyOpen=3
PolyLine=24,24
PolyLine=24,12
PolyLine=14,2

[shapedef]
Name=Capacitor
Line=0,0,22,0
Line=22,-8,22,8
Line=26,-8,26,8
Line=26,0,48,0
Current=32,12,16,12

[shapedef]
Name=Ground
Line=0,0,12,0
Line=12,-8,12,8
Line=18,-4,18,4
Line=24,0,24,0

[shapedef]
Name=Inductor
Line=42,0,48,0
Line=0,0,5,0
Arc=5,-7,17,7 , 11,-7,5,0
Arc=13,-7,25,7 , 19,-7,13,0
Arc=29,-7,41,7 , 35,-7,29,0
Arc=21,-7,33,7 , 27,-7,21,0
Arc=6,-7,18,7 , 18,0,12,-7
Arc=14,-7,26,7 , 26,0,20,-7
Arc=22,-7,34,7 , 34,0,28,-7
Arc=30,-7,42,7 , 42,0,36,-7
Line=11,-7,12,-7
Line=19,-7,20,-7
Line=27,-7,28,-7
Line=35,-7,36,-7
Arc=13,-4,17,2 , 13,-1,15,2
Arc=29,-4,33,2 , 29,-1,31,2
Arc=21,-4,25,2 , 21,-1,23,2
Arc=14,-4,18,2 , 16,2,18,-1
Arc=30,-4,34,2 , 32,2,34,-1
Arc=22,-4,26,2 , 24,2,26,-1
Line=15,2,16,2
Line=23,2,24,2
Line=31,2,32,2
Line=5,5,9,5
Line=41,5,41,9
Line=39,7,43,7
Current=32,8,16,8

[shapedef]
Name=NPN
Root="Bjt.root",0,0,0
PolyClosed=3
PolyLine=20,12
PolyLine=24,12
PolyLine=24,8

[shapedef]
Name=Resistor
PolyOpen=12
PolyLine=0,0
PolyLine=0,0
PolyLine=12,0
PolyLine=14,-4
PolyLine=18,4
PolyLine=22,-4
PolyLine=26,4
PolyLine=30,-4
PolyLine=34,4
PolyLine=36,0
PolyLine=48,0
PolyLine=48,0
Current=32,8,16,8

[compdef]
Name=Ground
Definition=Ground
Shape=Ground
Mask=1793
Used=345
memo=Ground
Label Offset=0,0,0,0
PinCnt=1
Pin="PinA",0,0,-3,-7

[compdef]
Name=Battery
Definition=Battery
Shape=Battery
Mask=7937
Used=59
memo=Battery
Label Offset=19,7,10,13
PinCnt=2
Pin="Plus",6,0,-4,-5
Pin="Minus",0,0,-10,-5

[compdef]
Name=Resistor
Definition=Resistor
Shape=Resistor
Mask=6913
Used=207
memo=Resistor
Label Offset=18,6,8,11
PinCnt=2
Pin="Plus",6,0,-10,-4
Pin="Minus",0,0,-14,-4

[compdef]
Name=Capacitor
Definition=Capacitor
Shape=Capacitor
Mask=7681
Used=97
memo=Capacitor
Label Offset=16,12,12,12
PinCnt=2
Pin="Plus",6,0,-3,-5
Pin="Minus",0,0,-14,-5

[compdef]
Name=Inductor
Definition=Inductor
Shape=Inductor
Mask=6401
Used=44
memo=Inductor
Label Offset=18,9,11,12
PinCnt=2
Pin="Plus",6,0,-5,-9
Pin="Minus",0,0,-3,-9

[compdef]
Name=NPN
Definition=NPN
Shape=NPN
Mask=5633
Used=39
memo=NPN Transistor
Label Offset=37,-17,-14,33
PinCnt=3
Pin="Collector",3,-3,4,14
Pin="Base",0,0,-18,-3
Pin="Emitter",3,3,5,1

[Circuit]
Window Placement=2,3, -1,-1, -8,-31, 52,52,1239,500
Default Object=Color=#000080
Default Object Font=Height=-15,FStyle=0,Color=#000080,Name=Arial
Default Object Apply Border To Text=No
Default Object Apply Fill To Text=No
Default Object GridSnap=No
NodeVoltageFormat=3
CurrentFormat=3
PowerFormat=3
PathDelayFormat=3
WarningFormat=3
GridTextFormulaFormat=3
Window Placement in Transient Analysis=2,3, -1,-1, -8,-31, 78,78,1461,526
Window Placement in Transient Probe=0,1, -1,-1, -8,-31, 0,0,1587,652
Window Placement in AC Analysis=2,3, -1,-1, -8,-31, 130,130,1513,578
Window Placement in DC Probe=0,1, -1,-1, -8,-31, 793,0,1586,652
SpiceType=AMBIGUOUS
Title_Block_Border=None
Title_Block=False
Show Nodes=False
Show Voltages=False
Show Current=False
Show Power=False
Show Condition=False
Show Pin Connections=False
Show Connection Warnings=False
Show Cross=False
Show Attribute Text=True
Show Grid Text=True

[Comp]
Name=Ground
Px=424,464
Rot=7

[Comp]
Name=Battery
Px=848,240
Rot=5
COff=8,811,206,-13,-17

[Attr]
ON=-37,-34,PART
V=V1
Style=8192

[Attr]
ON=-19,-20,VALUE
V=6
Style=8192

[Attr]
ON=0,0,PACKAGE
V

[Comp]
Name=Battery
Px=848,416
Rot=5
COff=8,813,381,-9,51

[Attr]
ON=-35,-35,PART
V=V2
Style=8192

[Attr]
ON=-26,-16,VALUE
V=6
Style=8192

[Attr]
ON=0,0,PACKAGE
V

[Comp]
Name=Resistor
Px=600,368
Rot=3

[Attr]
ON=-24,-25,PART
V=R2
Style=8192

[Attr]
ON=-23,-39,RESISTANCE
V=1k
Style=8192

[Attr]
ON=0,0,PACKAGE
V

[Comp]
Name=Resistor
Px=440,312
Rot=3

[Attr]
ON=9,-23,PART
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
Px=672,264
Rot=7

[Comp]
Name=Capacitor
Px=904,248
Rot=7

[Attr]
ON=-41,12,PART
V=C1
Style=8192

[Attr]
ON=-44,26,CAPACITANCE
V=0.1u
Style=8192

[Attr]
ON=0,0,PACKAGE
V

[Comp]
Name=Capacitor
Px=968,248
Rot=7

[Attr]
ON=-41,12,PART
V=C3
Style=8192

[Attr]
ON=-52,26,CAPACITANCE
V=0.01u
Style=8192

[Attr]
ON=0,0,PACKAGE
V

[Comp]
Name=Capacitor
Px=1040,248
Rot=7

[Attr]
ON=-41,12,PART
V=C5
Style=8192

[Attr]
ON=-60,26,CAPACITANCE
V=0.001u
Style=8192

[Attr]
ON=0,0,PACKAGE
V

[Wire]
Pxs=904,304,968,304

[Wire]
Pxs=968,304,1040,304

[Comp]
Name=Ground
Px=816,304
Rot=7

[Comp]
Name=Capacitor
Px=904,304
Rot=7

[Attr]
ON=-41,12,PART
V=C2
Style=8192

[Attr]
ON=-44,26,CAPACITANCE
V=0.1u
Style=8192

[Attr]
ON=0,0,PACKAGE
V

[Comp]
Name=Capacitor
Px=968,304
Rot=7

[Attr]
ON=-41,12,PART
V=C4
Style=8192

[Attr]
ON=-52,26,CAPACITANCE
V=0.01u
Style=8192

[Attr]
ON=0,0,PACKAGE
V

[Comp]
Name=Capacitor
Px=1040,304
Rot=7

[Attr]
ON=-41,12,PART
V=C6
Style=8192

[Attr]
ON=-60,26,CAPACITANCE
V=0.001u
Style=8192

[Attr]
ON=0,0,PACKAGE
V

[Wire]
Pxs=904,296,904,304

[Wire]
Pxs=968,296,968,304

[Wire]
Pxs=1040,296,1040,304

[Wire]
Pxs=816,304,848,304

[Wire]
Pxs=904,352,968,352

[Wire]
Pxs=968,352,1040,352

[Wire]
Pxs=968,248,1040,248

[Wire]
Pxs=904,248,968,248

[Wire]
Pxs=848,416,848,424

[Wire]
Pxs=848,424,848,488

[Wire]
Pxs=848,304,848,368

[Wire]
Pxs=848,128,1040,128

[Wire]
Pxs=1040,128,1040,248

[Wire]
Pxs=1040,352,1040,488

[Wire]
Pxs=848,488,1040,488

[Wire]
Pxs=848,304,904,304

[Wire]
Pxs=720,352,720,360

[Wire]
Pxs=720,320,720,352

[Wire]
Pxs=776,320,776,360

[Wire]
Pxs=752,320,776,320

[Wire]
Pxs=376,216,504,216

[Grid Text]
Text="Vee"
Px=848,424
GridSnap=True
JustifyH=Left
JustifyV=Bottom
CBorder=None

[Grid Text]
Text="Vcc"
Px=848,192
GridSnap=True
JustifyH=Left
JustifyV=Bottom
CBorder=None

[Grid Text]
Text="Vsal"
Px=752,320
GridSnap=True
JustifyH=Left
JustifyV=Bottom
CBorder=None

[Grid Text]
Text="Vcol"
Px=720,216
GridSnap=True
JustifyH=Left
JustifyV=Bottom
CBorder=None

[Schematic]
CurrentSection 0=0
CurrentSection 1=0
CurrentSection 2=0
CurrentSection 3=0
Splitter.xs=0
Splitter.ys=0
TextQuad=4099
Scale=0.5
GridUser=10
ShapeGroups="Main","Euro","Polarity","Main1","Main11","Electrolytic","GroundArrow","DeMorgan"
CalcRMS=False
CalcAVG=False
CalcPeak=False
CalcVoltage=True
DisplayMeasure=Last
ShareScales=True

[Tools]
Pos=Top
FILESAVEASOLD=No
BOM=No
FILEPCB=No
PROBE=Yes
SELECT=Yes
PAN=Yes
COMP=Yes
TEXT=Yes
WIRE=Yes
WIRED=Yes
BUS=Yes
GRAPHIC=Yes
FLOWCHART=Yes
LINE=No
ELLIPSE=No
RECT=No
DIAM=No
ARC=No
PIE=No
TRIANGLE=No
STAR=No
LEFTBRK=No
RIGHTBRK=No
BOTHBRK=No
META=No
PARALLELOGRAM=No
FC_PROCESS=No
FC_ALT_PROCESS=No
FC_DECISION=No
FC_DATA=No
FC_PREDEFPROCESS=No
FC_INTERNALSTORAGE=No
FC_DOCUMENT=No
FC_MULTIDOCUMENT=No
FC_TERMINATOR=No
FC_PREPARATION=No
FC_MANUALINPUT=No
FC_MANUALOPERATION=No
FC_CONNECTOR=No
FC_OFFPAGECONNECTOR=No
FC_PUNCHCARD=No
FC_PUNCHEDTAPE=No
FC_SUMMING_JUNCTION=No
FC_OR=No
FC_COLLATE=No
FC_SORT=No
FC_EXTRACT=No
FC_MERGE=No
FC_STORED_DATA=No
FC_DELAY=No
FC_SAS=No
FC_MAGNETIC_DISK=No
FC_DAS=No
FC_DISPLAY=No
SPREAD_SHEET=Yes
POLYCLOS=No
POLYOPEN=No
FLAG=Yes
INFO=Yes
HELP=Yes
HELP_SPICE=No
LINK=Yes
CHECK=Yes
REGION_ENABLE=Yes
TITLE_BLOCK=Yes
DIGTRC=No
DIGTRC2=No
BUILD_COMMAND=Yes
DIGALL=No
GRIDTEXT=Yes
COMPTEXT=Yes
NODE=Yes
MEASURED=Yes
NODEV=Yes
CURRENT=Yes
POWER=Yes
CONDITIN=Yes
PIN=Yes
CONNWARN=Yes
CROSS=No
GRID=Yes
BORDER=Yes
BORDERONE=Yes
TITLE=Yes
RUBBER=Yes
PROPERTY=Yes
STEP=Yes
MIRROR=Yes
ROTATE=Yes
FLIPY=Yes
FLIPX=Yes
CIR_MAKEMACRO=No
CLEARCUTWIRE=No
CLIPBOARDCIRPAGE2BMM=No
FINDCOMP=Yes
FIND=Yes
REPEAT=No
REPLACE=No
MODEL=Yes
CIR2CKT=No
ATTDISP=No
ENABLE=Yes
DISABLE=Yes
ENABLE_WITH=Yes
TOFRONT=Yes
TOBACK=Yes
SELNEXT=No
PAGEADD=No
PAGEADDTEXT=No
ADDSECTION=No
PAGEDEL=No
ZOOMIN=Yes
ZOOMOUT=Yes
AUTOSCALECIR=Yes
GOTOFLAG=No
UPLEVEL=Yes
COLOR=Yes
FONT=Yes
STYLE=Yes
DM_LAST=No
DM_RMS=No
DM_AVG=No
DM_PEAK=No
GRID_NONE=No
GRID_NORMAL=No
GRID_BOLD_5=No
GRID_BOLD_6=No
GRID_BOLD_USER=No
GRAPH_PAPER=No
SPLITCIRTEXTH=No
SPLITCIRTEXTV=No
SPACE_SPLITTERS_EVENLY=No
NORMALCIR=No
RENAMEDEFINE=No
RENAMECMP=No
ATTALIGN=No
RESETNODEPOS=No
FIT2STANDARD=No
NODESNAP=No
MOVETEXT=No
TEXTINC=No
TOGGLETEXT=No
TOGGLEMODE=No
TOLERANCE=No
ALIGNAB=No
ALIGNLEFT=No
ALIGNCENTER=No
ALIGNRIGHT=No
ALIGNTOP=No
ALIGNMIDDLES=No
ALIGNBOTTOM=No

[Section]
Index=0
Name="Oscilador real con capacitor variable medido en FRA"
Type=Main
Enable=True
CurrentPage 0=0
CurrentPage 1=0
CurrentPage 2=0
CurrentPage 3=0
TabSize 0=425
TabSize 1=425
TabSize 2=425
TabSize 3=425

[Page]
Index=0
Section=0
Print=True
Enable=True
Name=Main
PrinterScale=1
Scale 0=1
Scale 1=1
Scale 2=1
SB 3=302,117
Scale 3=0.5
Px=744,317
WinBackGround Color=#FFFFFF
Select Color=#FF0000
Anchor Color=#000000
Select Box Color=#000080
Grid Text Color=Height=-12,FStyle=0,Color=#0000FF,Name=Verdana
Grid Text RTF=False
Grid Text Angle=0
Grid Text GridSnap=True
Grid Text PinIt=False
Grid Text JustifyH=Left
Grid Text JustifyV=Bottom
Grid GradientColor2=None
Grid OutlineThickness=1
Grid OutlineColor=None
Component Color=#0000FF
Attribute Text=Height=-12,FStyle=0,Color=#008000,Name=Verdana
Wire Color=#008000
Bus Color=#008000
Pin Connection=Height=-10,FStyle=0,Color=#FF0000,Name=Arial
Pin Marker Color=#008000
Node Number=Height=-11,FStyle=0,Color=#FF00FF,Name=Arial
Node Voltage Color=Height=-11,FStyle=0,Color=#000000,Name=Arial
Dynamic AC Voltage Color=#E4E4E4
Text Banner Text=Height=-15,FStyle=0,Color=#800000,Name=Arial
Title Block Background=#C0C0C0
Current=Height=-11,FStyle=0,Color=#0000FF,Name=Arial
Power/Condition=Height=-11,FStyle=0,Color=#FF0000,Name=Arial
Digital Path Color=#FF0000
Title Block Border=#000000
Disabled	Color=#C0C0C0
Search Color=#FFFF00
Grid Color=#000000
Graph Paper=#E4E4E4
Digital 0 Color=#000000
Digital R Color=#FFFF00
Digital F Color=#FFFF00
Digital 1 Color=#FF0000
Digital X Color=#C0C0C0
Digital Z Color=#808080
Block Select Color=#51F998

[Page]
Index=1
Section=0
Type=Text
Print=False
Enable=True
Name=Text
Font=Height=-15,FStyle=0,Color=#000000,Name=Courier New
Comment Color=#008000
WinBackGround Color=#FFFFFF
Disabled	Color=#C0C0C0
KeyWord Color=#0000FF
Error	Color=#FF0000
Search Color=#FFFF00

[Page]
Index=2
Section=0
Type=Text
Print=False
Enable=True
Name=Models
Font=Height=-15,FStyle=0,Color=#000000,Name=Courier New
Comment Color=#008000
WinBackGround Color=#FFFFFF
Disabled	Color=#C0C0C0
KeyWord Color=#0000FF
Error	Color=#FF0000
Search Color=#FFFF00

[Page]
Index=3
Section=0
Type=Info
Print=False
Enable=True
Name=Info
Font=Height=-15,FStyle=0,Color=#000000,Name=Courier New
Comment Color=#008000
WinBackGround Color=#FFFFFF
Disabled	Color=#C0C0C0
KeyWord Color=#0000FF
Error	Color=#FF0000
Search Color=#FFFF00

[Text Area]
Section=0
Page=1
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
